hannahsq/PPS-50-DT/schematics/gpib_controller.kicad_sch

## KiCad design schematics/gpib_controller.kicad_sch (2026-04-03, an earlier design)

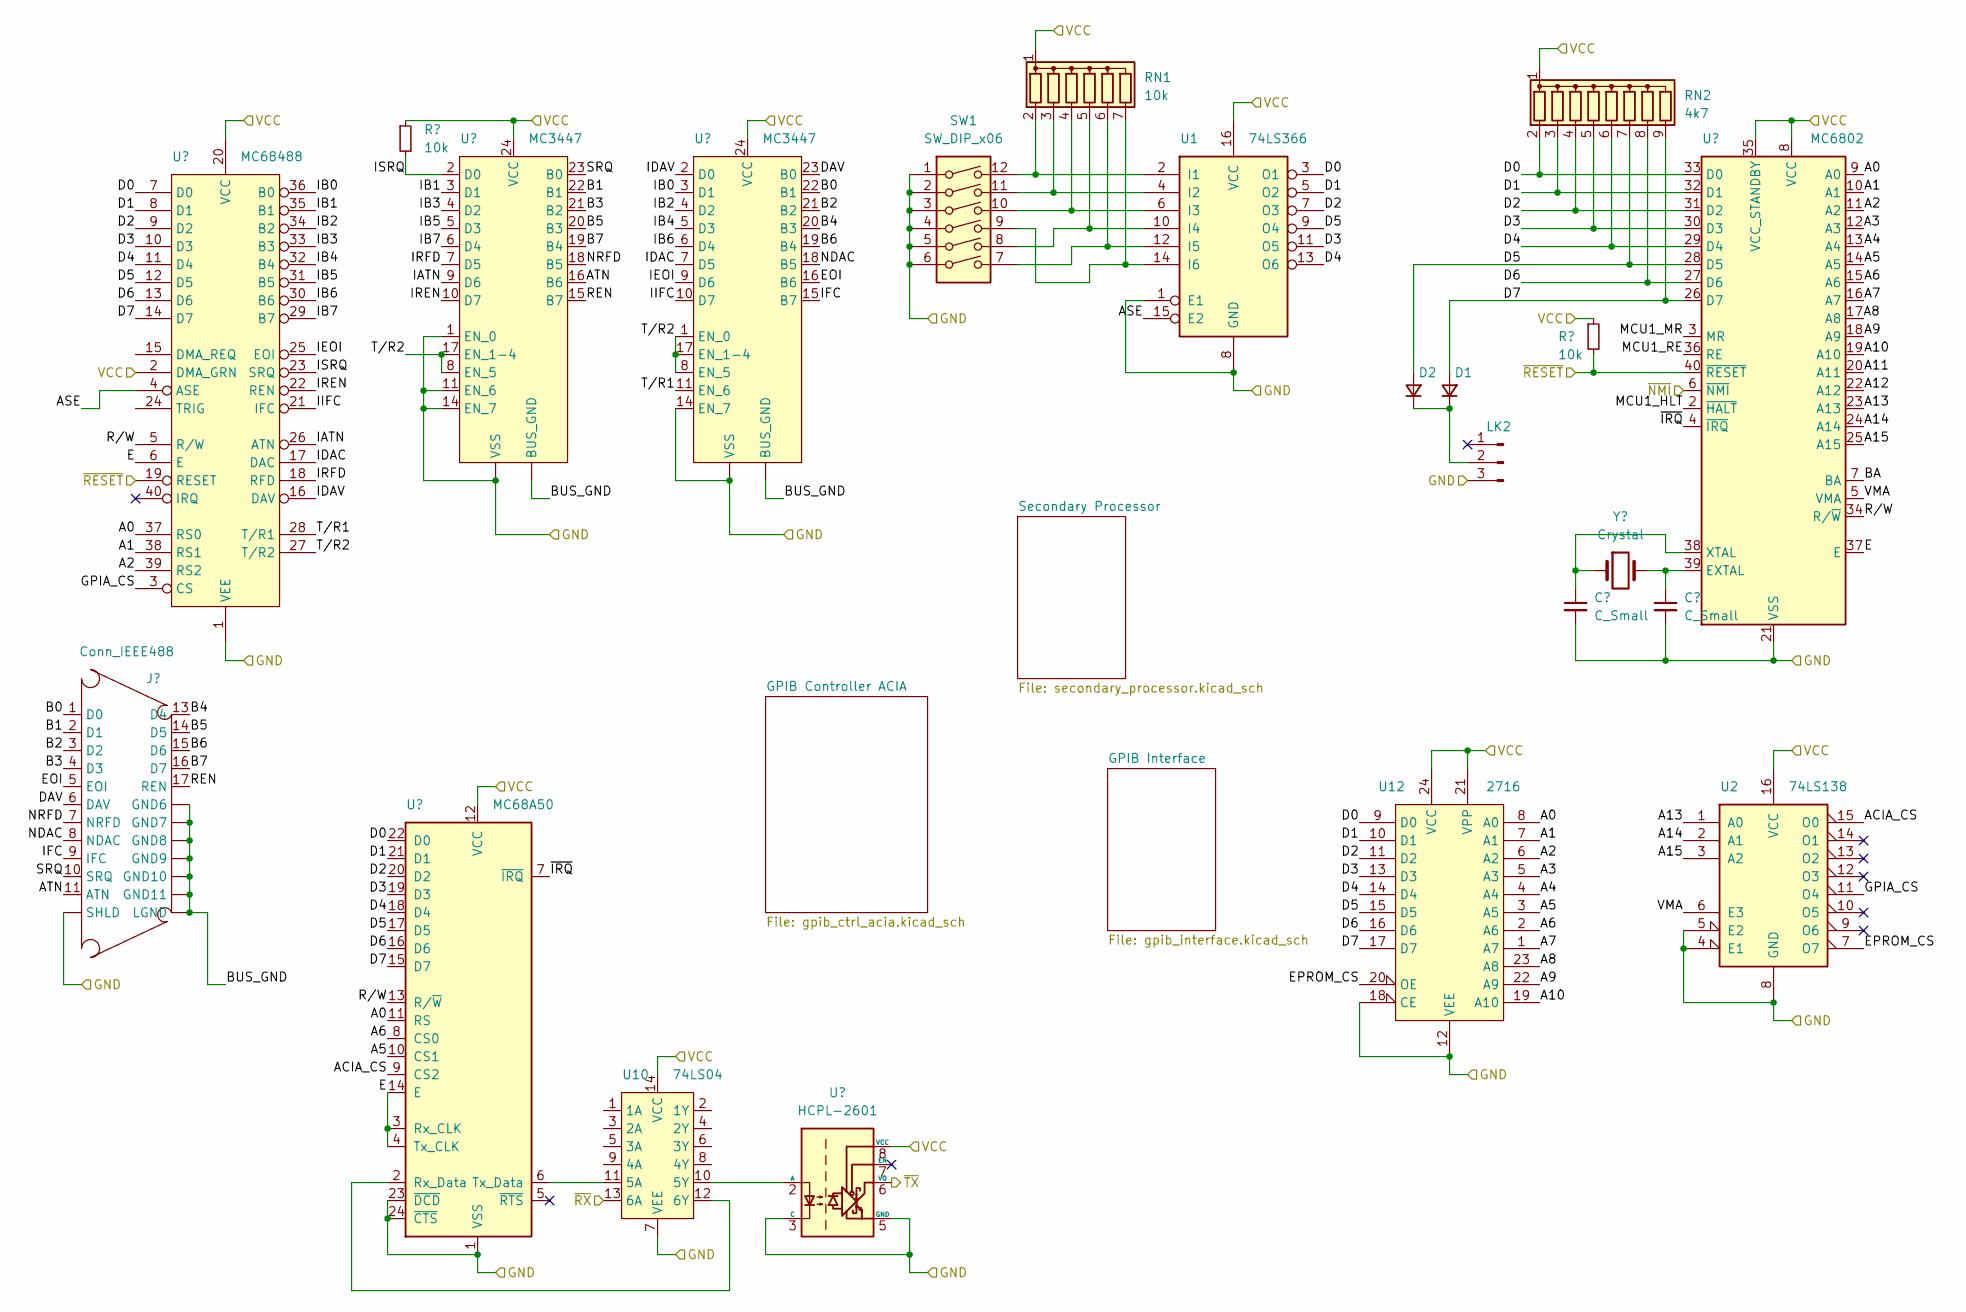
[picture p24: schematic gpib_controller.kicad_sch]

Parts:
D1, D2: D_Small
LK2: Conn_01x03_Male
RN1: 10k; R_Array_SIP7
RN2: 4k7; R_Array_SIP9
SW1: SW_DIP_x06
U1: 74LS366
U2: 74LS138
U10: 74LS04
U12: 2716

Connections:
A0: U12.8 (A0)
A1: U12.7 (A1)
A2: U12.6 (A2)
A3: U12.5 (A3)
A4: U12.4 (A4)
A5: U12.3 (A5)
A6: U12.2 (A6)
A7: U12.1 (A7)
A8: U12.23 (A8)
A9: U12.22 (A9)
A10: U12.19 (A10)
A13: U2.1 (A0)
A14: U2.2 (A1)
A15: U2.3 (A2)
ACIA_CS: U2.15 (O0)
ASE: U1.15 (E2)
D0: RN2.2 (R1), U1.3 (O1), U12.9 (D0)
D1: RN2.3 (R2), U1.5 (O2), U12.10 (D1)
D2: RN2.4 (R3), U1.7 (O3), U12.11 (D2)
D3: RN2.5 (R4), U1.11 (O5), U12.13 (D3)
D4: RN2.6 (R5), U1.13 (O6), U12.14 (D4)
D5: D2.2 (A), RN2.7 (R6), U1.9 (O4), U12.15 (D5)
D6: RN2.8 (R7), U12.16 (D6)
D7: D1.2 (A), RN2.9 (R8), U12.17 (D7)
EPROM_CS: U2.7 (O7), U12.20 (OE)
GND: LK2.3, SW1.1, SW1.2, SW1.3, SW1.4, SW1.5, SW1.6, U1.1 (E1), U1.8 (GND), U2.4 (E1), U2.5 (E2), U2.8 (GND), U10.7 (VEE), U12.12 (VEE), U12.18 (CE)
GPIA_CS: U2.11 (O4)
unnamed: D1.1 (K), D2.1 (K), LK2.2
unnamed: RN1.2 (R1), SW1.12, U1.2 (I1)
unnamed: RN1.3 (R2), SW1.11, U1.4 (I2)
unnamed: RN1.4 (R3), SW1.10, U1.6 (I3)
unnamed: RN1.5 (R4), SW1.8, U1.10 (I4)
unnamed: RN1.6 (R5), SW1.7, U1.12 (I5)
unnamed: RN1.7 (R6), SW1.9, U1.14 (I6)
VCC: RN1.1 (common), RN2.1 (common), U1.16 (VCC), U2.16 (VCC), U10.14 (VCC), U12.21 (VPP), U12.24 (VCC)
VMA: U2.6 (E3)
~RX: U10.13 (6A)
