hannahsq/PPS-50-DT/schematics/rect_and_reg.kicad_sch

## KiCad design schematics/rect_and_reg.kicad_sch (2024-05-18)

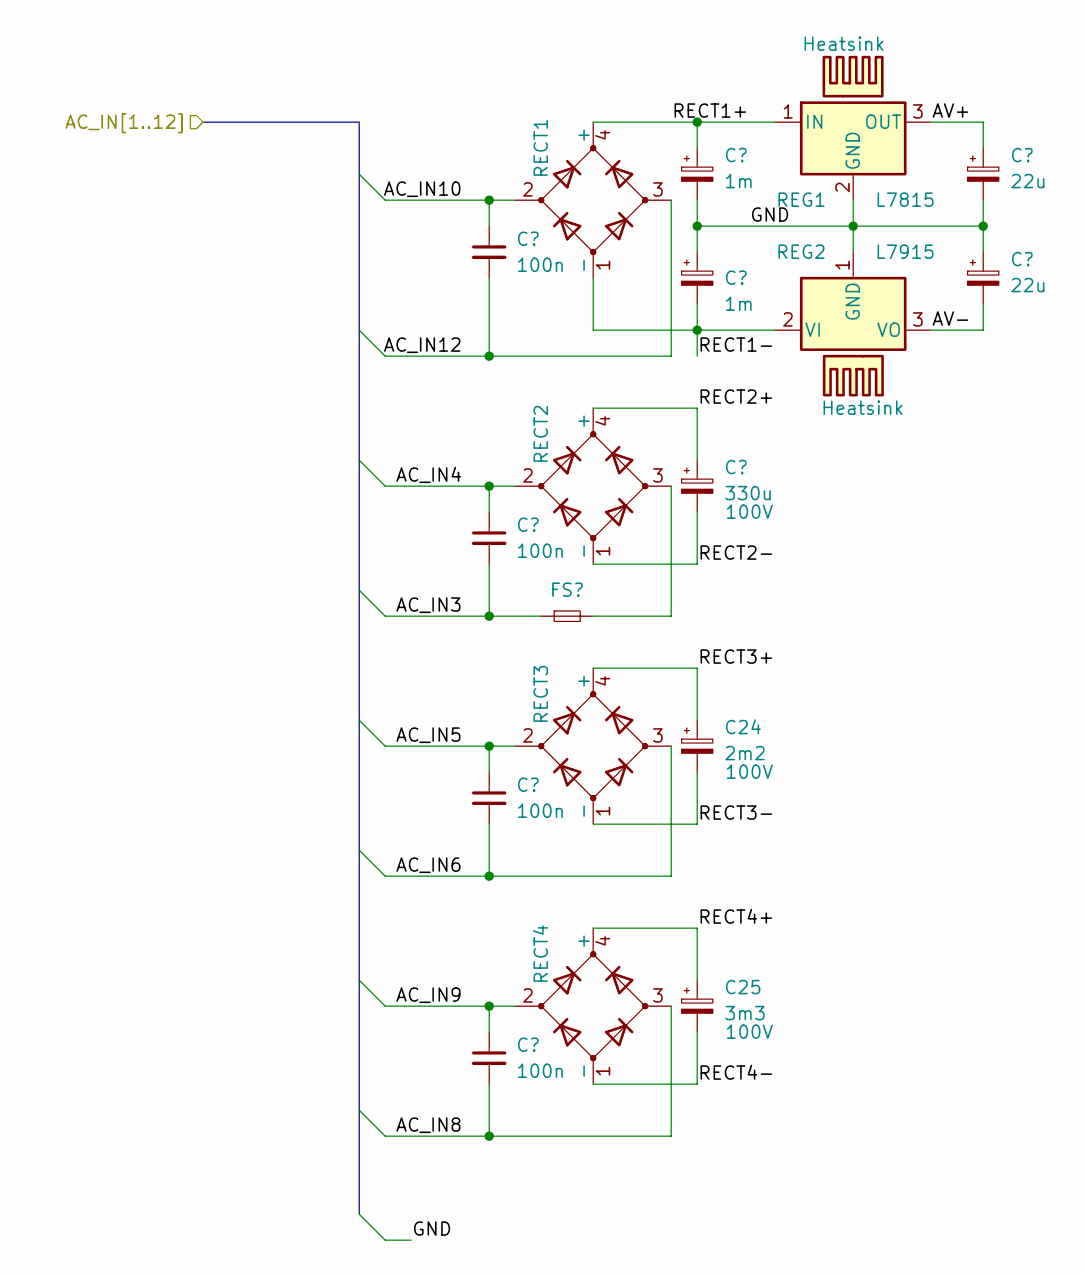
[picture p26: schematic rect_and_reg.kicad_sch]

Parts:
C24: 2m2; Voltage 100V
C25: 3m3; Voltage 100V
RECT1, RECT2, RECT3, RECT4: D_Bridge_-AA+
REG1: L7815
REG2: L7915

Connections:
AC_IN4: RECT2.2
AC_IN5: RECT3.2
AC_IN6: RECT3.3
AC_IN8: RECT4.3
AC_IN9: RECT4.2
AC_IN10: RECT1.2
AC_IN12: RECT1.3
AV+: REG1.3 (OUT)
AV-: REG2.3 (VO)
GND: REG1.2 (GND), REG2.1 (GND)
RECT1+: RECT1.4 (+), REG1.1 (IN)
RECT1-: RECT1.1 (-), REG2.2 (VI)
RECT2+: RECT2.4 (+)
RECT2-: RECT2.1 (-)
RECT3+: C24.1, RECT3.4 (+)
RECT3-: C24.2, RECT3.1 (-)
RECT4+: C25.1, RECT4.4 (+)
RECT4-: C25.2, RECT4.1 (-)
