hannahsq/PPS-50-DT/asm/primary_controller.asm

; f9dasm: M6800/1/2/3/8/9 / H6309 Binary/OS9/FLEX9 Disassembler V1.83
; Loaded binary file primary_controller.bin

;****************************************************
;* Used Labels                                      *
;****************************************************

irq_prescaler EQU     $0000
debounce_timer EQU     $0001
key_repeat_timer EQU     $0002
output_update_pending EQU     $0003
watchdog_counter EQU     $0004
tick_counter EQU     $0005
cha_voltage_set_hi EQU     $0006
cha_voltage_set_lo EQU     $0007
cha_current_set_hi EQU     $0008
cha_voltage_limit_hi EQU     $000A
cha_current_limit_hi EQU     $000C
cha_vs_shadow_hi EQU     $000E
cha_vs_shadow_lo EQU     $000F
cha_is_shadow_hi EQU     $0010
cha_is_shadow_lo EQU     $0011
chb_voltage_set_hi EQU     $0012
chb_current_set_hi EQU     $0014
chb_voltage_limit_hi EQU     $0016
chb_current_limit_hi EQU     $0018
chb_vs_shadow_hi EQU     $001A
chb_vs_shadow_lo EQU     $001B
chb_is_shadow_hi EQU     $001C
chb_is_shadow_lo EQU     $001D
adc_digit_0 EQU     $001E
adc_digit_1 EQU     $001F
adc_digit_2 EQU     $0020
adc_digit_3 EQU     $0021
adc_digit_4 EQU     $0022
adc_mux_channel EQU     $0023
dac_out_cha_v EQU     $0024
dac_out_cha_i EQU     $0025
dac_out_chb_v EQU     $0026
dac_out_chb_i EQU     $0027
dac_out_cha_vl EQU     $0028
dac_out_cha_il EQU     $0029
dac_out_chb_vl EQU     $002A
dac_out_chb_il EQU     $002B
dac_mux_ptr_hi EQU     $002C
M002D   EQU     $002D
dac_mux_select EQU     $002E
cha_fb_voltage_hi EQU     $002F
cha_fb_voltage_lo EQU     $0030
cha_fb_current_hi EQU     $0031
chb_fb_voltage_hi EQU     $0033
chb_fb_voltage_lo EQU     $0034
chb_fb_current_hi EQU     $0035
uart_timeout_lo EQU     $0037
uart_timeout_hi EQU     $0038
acia_rx_cmd EQU     $0039
acia_rx_data_hi EQU     $003A
acia_rx_data_lo EQU     $003B
math_temp_hi EQU     $003C
math_temp_lo EQU     $003D
acia_tx_cmd EQU     $003E
acia_tx_data_hi EQU     $003F
acia_tx_data_lo EQU     $0040
gpib_link_active EQU     $0041
reinit_requested EQU     $0042
keycode_or_adcmode EQU     $0043
key_state_flags EQU     $0044
scan_column_index EQU     $0045
scan_column_mask EQU     $0046
scan_result_offset EQU     $0047
scan_hit_count EQU     $0048
polarity_sign EQU     $0049
cmd_state_step EQU     $004A
digit_buf_0 EQU     $004B
digit_buf_1 EQU     $004C
digit_buf_2 EQU     $004D
digit_buf_3 EQU     $004E
decimal_point_pos EQU     $004F
digit_count EQU     $0050
channel_mode_state EQU     $0051
cmd_flags EQU     $0052
device_state EQU     $0053
status_pending EQU     $0054
status_confirmed EQU     $0055
uart_frame_type EQU     $0056
dac_mux_shadow EQU     $0057
display_port_shadow EQU     $0058
math_work_hi EQU     $0059
math_work_lo EQU     $005A
temp_ptr_hi EQU     $005B
temp_ptr_lo EQU     $005C
temp_counter EQU     $005D
indirect_ptr_hi EQU     $005E
indirect_ptr_lo EQU     $005F
dac_scale_result EQU     $0060
scale_input_hi EQU     $0061
scale_input_lo EQU     $0062
acia_inhibit_timer EQU     $0063
status_send_delay EQU     $0064
status_toggle EQU     $0065
dac_update_mask EQU     $0066
dac_settle_timer EQU     $0067
display_scan_index EQU     $0068
M007F   EQU     $007F
DAC_LATCH EQU     $0080
IC20_PRA EQU     $0090
IC20_CRA EQU     $0091
IC20_PRB EQU     $0092
IC20_CRB EQU     $0093
IC18_PRA EQU     $00A0
IC18_CRA EQU     $00A1
IC18_PRB EQU     $00A2
IC18_CRB EQU     $00A3
AMUX_SELECT EQU     $00C0
ACIA_CSR EQU     $00D0
ACIA_DR EQU     $00D1
IC19_PRA EQU     $00E0
IC19_CRA EQU     $00E1
IC19_PRB EQU     $00E2
IC19_CRB EQU     $00E3
M03E8   EQU     $03E8
M05DC   EQU     $05DC
range_threshold_50V EQU     $0898
M09F4   EQU     $09F4
M0F0F   EQU     $0F0F
range_threshold_25V EQU     $1130
M8F8F   EQU     $8F8F
MA4F0   EQU     $A4F0
MC7F0   EQU     $C7F0
MCEF1   EQU     $CEF1

;****************************************************
;* Program Code / Data Areas                        *
;****************************************************

        ORG     $E000

; === ACIA INTERRUPT HANDLER ===
; Increment GPIB activity counter (M0x04)
hdlr_ACIA_IRQ LDAA    watchdog_counter         ;E000: 96 04          '..'
        CMPA    #$FF                     ;E002: 81 FF          '..'
        BLS     ZE008                    ;E004: 23 02          '#.'
        BRA     ZE00B                    ;E006: 20 03          ' .'

ZE008   INC     >watchdog_counter        ;E008: 7C 00 04       '|..'
; Set ACIA inhibit timer to 0x14
ZE00B   LDAA    #$14                     ;E00B: 86 14          '..'
        STAA    acia_inhibit_timer       ;E00D: 97 63          '.c'
        LDAA    #$11                     ;E00F: 86 11          '..'
; Disable ACIA RX interrupts temporarily
        STAA    >ACIA_CSR                ;E011: B7 00 D0       '...'
; Read received data byte from ACIA
        LDAA    >ACIA_DR                 ;E014: B6 00 D1       '...'
; Decode frame type (bits 3:2 determine status/data/cmd)
        JSR     decode_uart_frame_type   ;E017: BD E0 53       '..S'
        LDAB    uart_frame_type          ;E01A: D6 56          '.V'
; Send acknowledgment byte back to GPIB controller
        JSR     acia_send_byte           ;E01C: BD E0 99       '...'
        BNE     hdlr_ACIA_RTI            ;E01F: 26 28          '&('
; Receive 3-byte command from GPIB controller
        JSR     acia_recv_3_bytes        ;E021: BD E0 79       '..y'
        BNE     hdlr_ACIA_RTI            ;E024: 26 23          '&#'
; Load command byte
        LDAA    acia_rx_cmd              ;E026: 96 39          '.9'
; Check for 'q' (0x71) - query command
        CMPA    #$71                     ;E028: 81 71          '.q'
; Check for status commands: 'S'(0x53), 'T'(0x54), 'q'(0x71)
; These commands clear the GPIB link active flag
        BEQ     ZE037                    ;E02A: 27 0B          ''.'
        CMPA    #$53                     ;E02C: 81 53          '.S'
        BEQ     ZE037                    ;E02E: 27 07          ''.'
        CMPA    #$54                     ;E030: 81 54          '.T'
        BEQ     ZE037                    ;E032: 27 03          ''.'
        CLR     >gpib_link_active        ;E034: 7F 00 41       '..A'
; Reset command state variables
ZE037   JSR     reset_cmd_state          ;E037: BD F3 EA       '...'
; Clear command step counter
        CLR     >cmd_state_step          ;E03A: 7F 00 4A       '..J'
; Process command and build response
        JSR     process_gpib_command     ;E03D: BD E0 EE       '...'
; Send 3-byte response back to GPIB controller
        JSR     acia_send_3_bytes        ;E040: BD E0 CE       '...'
; Clear channel mode state bits
        CLR     >channel_mode_state      ;E043: 7F 00 51       '..Q'
        CLR     >cmd_flags               ;E046: 7F 00 52       '..R'
; Re-enable ACIA RX interrupts (write 0x91 to CSR)
hdlr_ACIA_RTI LDAA    #$00                     ;E049: 86 00          '..'
        LDAA    #$91                     ;E04B: 86 91          '..'
        STAA    >ACIA_CSR                ;E04D: B7 00 D0       '...'
; Return from interrupt
        JMP     hdlr_RTI                 ;E050: 7E E5 79       '~.y'

; === DECODE UART FRAME TYPE FROM RX BITS 3:2 ===
; Bits 3:2 == 00: normal data (frame_type = 0)
decode_uart_frame_type ANDA    #$0C                     ;E053: 84 0C          '..'
        BNE     ZE05C                    ;E055: 26 05          '&.'
        CLR     >uart_frame_type         ;E057: 7F 00 56       '..V'
        BRA     ZE078                    ;E05A: 20 1C          ' .'

; Bits 3:2 == 10: status update (frame_type = 1)
ZE05C   CMPA    #$08                     ;E05C: 81 08          '..'
        BNE     ZE066                    ;E05E: 26 06          '&.'
        LDAA    #$01                     ;E060: 86 01          '..'
        STAA    uart_frame_type          ;E062: 97 56          '.V'
        BRA     ZE078                    ;E064: 20 12          ' .'

; Bits 3:2 == 11: status + data (frame_type = 3)
ZE066   CMPA    #$0C                     ;E066: 81 0C          '..'
        BNE     ZE070                    ;E068: 26 06          '&.'
        LDAA    #$03                     ;E06A: 86 03          '..'
        STAA    uart_frame_type          ;E06C: 97 56          '.V'
        BRA     ZE078                    ;E06E: 20 08          ' .'

; Bits 3:2 == 01: data only (frame_type = 2)
ZE070   CMPA    #$04                     ;E070: 81 04          '..'
        BNE     ZE078                    ;E072: 26 04          '&.'
        LDAA    #$02                     ;E074: 86 02          '..'
        STAA    uart_frame_type          ;E076: 97 56          '.V'
ZE078   RTS                              ;E078: 39             '9'

;-------------------------------------------------------------------------------

; === RECV 3 BYTES FROM ACIA ===
; Receive bytes into acia_rx_cmd, acia_rx_data_hi, acia_rx_data_lo
; Returns Z=1 on success, Z=0 on timeout/error
acia_recv_3_bytes JSR     acia_recv_byte           ;E079: BD E0 B1       '...'
        BNE     ZE095                    ;E07C: 26 17          '&.'
        STAB    >acia_rx_cmd             ;E07E: F7 00 39       '..9'
        JSR     acia_recv_byte           ;E081: BD E0 B1       '...'
        BNE     ZE095                    ;E084: 26 0F          '&.'
        STAB    >acia_rx_data_hi         ;E086: F7 00 3A       '..:'
        JSR     acia_recv_byte           ;E089: BD E0 B1       '...'
        BNE     ZE095                    ;E08C: 26 07          '&.'
        STAB    >acia_rx_data_lo         ;E08E: F7 00 3B       '..;'
        CLRA                             ;E091: 4F             'O'
        JMP     ZE097                    ;E092: 7E E0 97       '~..'

ZE095   LDAA    #$FF                     ;E095: 86 FF          '..'
ZE097   TSTA                             ;E097: 4D             'M'
        RTS                              ;E098: 39             '9'

;-------------------------------------------------------------------------------

; === SEND BYTE VIA ACIA ===
; Wait for TX buffer empty, send byte from ACCB
acia_send_byte LDX     #uart_timeout_lo         ;E099: CE 00 37       '..7'
; Poll ACIA status for TDRE (bit 1)
ZE09C   LDAA    >ACIA_CSR                ;E09C: B6 00 D0       '...'
        ANDA    #$02                     ;E09F: 84 02          '..'
        BNE     ZE0AB                    ;E0A1: 26 08          '&.'
        DEX                              ;E0A3: 09             '.'
        BNE     ZE09C                    ;E0A4: 26 F6          '&.'
        LDAA    #$FF                     ;E0A6: 86 FF          '..'
        JMP     ZE0AF                    ;E0A8: 7E E0 AF       '~..'

; Write byte to ACIA data register
ZE0AB   STAB    >ACIA_DR                 ;E0AB: F7 00 D1       '...'
        CLRA                             ;E0AE: 4F             'O'
; Return Z=1 on success
ZE0AF   TSTA                             ;E0AF: 4D             'M'
        RTS                              ;E0B0: 39             '9'

;-------------------------------------------------------------------------------

; === RECV BYTE FROM ACIA ===
; Wait for RX buffer full, receive byte into ACCB
acia_recv_byte LDX     #uart_timeout_lo         ;E0B1: CE 00 37       '..7'
ZE0B4   LDAA    >ACIA_CSR                ;E0B4: B6 00 D0       '...'
        TAB                              ;E0B7: 16             '.'
        ANDA    #$01                     ;E0B8: 84 01          '..'
        BNE     ZE0C4                    ;E0BA: 26 08          '&.'
        DEX                              ;E0BC: 09             '.'
        BNE     ZE0B4                    ;E0BD: 26 F5          '&.'
; Return Z=0 on timeout
ZE0BF   LDAA    #$FF                     ;E0BF: 86 FF          '..'
        JMP     ZE0C9                    ;E0C1: 7E E0 C9       '~..'

; Return Z=0 on ACIA error
ZE0C4   ANDB    #$70                     ;E0C4: C4 70          '.p'
        BNE     ZE0BF                    ;E0C6: 26 F7          '&.'
        CLRA                             ;E0C8: 4F             'O'
; Return Z=1 on success
ZE0C9   LDAB    >ACIA_DR                 ;E0C9: F6 00 D1       '...'
        TSTA                             ;E0CC: 4D             'M'
        RTS                              ;E0CD: 39             '9'

;-------------------------------------------------------------------------------

; === SEND 3 BYTES VIA ACIA ===
; Send acia_tx_cmd, acia_tx_data_hi, acia_tx_data_lo
acia_send_3_bytes LDAB    >acia_tx_cmd             ;E0CE: F6 00 3E       '..>'
        JSR     acia_send_byte           ;E0D1: BD E0 99       '...'
        BNE     ZE0EA                    ;E0D4: 26 14          '&.'
        LDAB    >acia_tx_data_hi         ;E0D6: F6 00 3F       '..?'
        JSR     acia_send_byte           ;E0D9: BD E0 99       '...'
        BNE     ZE0EA                    ;E0DC: 26 0C          '&.'
        LDAB    >acia_tx_data_lo         ;E0DE: F6 00 40       '..@'
        JSR     acia_send_byte           ;E0E1: BD E0 99       '...'
        BNE     ZE0EA                    ;E0E4: 26 04          '&.'
        CLRA                             ;E0E6: 4F             'O'
        JMP     ZE0EC                    ;E0E7: 7E E0 EC       '~..'

ZE0EA   LDAA    #$FF                     ;E0EA: 86 FF          '..'
ZE0EC   TSTA                             ;E0EC: 4D             'M'
        RTS                              ;E0ED: 39             '9'

;-------------------------------------------------------------------------------

; === PROCESS GPIB COMMAND ===
; Copy RX buffer to TX buffer (echo command)
process_gpib_command LDAA    >acia_rx_cmd             ;E0EE: B6 00 39       '..9'
        STAA    >acia_tx_cmd             ;E0F1: B7 00 3E       '..>'
        LDAA    >acia_rx_data_hi         ;E0F4: B6 00 3A       '..:'
        STAA    >acia_tx_data_hi         ;E0F7: B7 00 3F       '..?'
        LDAA    >acia_rx_data_lo         ;E0FA: B6 00 3B       '..;'
        STAA    >acia_tx_data_lo         ;E0FD: B7 00 40       '..@'
; Test frame_type: if even, check for special commands
        LDAA    >uart_frame_type         ;E100: B6 00 56       '..V'
        ANDA    #$01                     ;E103: 84 01          '..'
        BNE     gpib_cmd_dispatch        ;E105: 26 18          '&.'
; Check for 'S' (0x53): serial poll �¨ enable remote
        LDAA    >acia_rx_cmd             ;E107: B6 00 39       '..9'
        CMPA    #$53                     ;E10A: 81 53          '.S'
        BEQ     ZE11A                    ;E10C: 27 0C          ''.'
; Check for 'U' (0x55): status update
        CMPA    #$55                     ;E10E: 81 55          '.U'
        BEQ     gpib_cmd_dispatch        ;E110: 27 0D          ''.'
; Check for 'V' (0x56): device clear
        CMPA    #$56                     ;E112: 81 56          '.V'
        BEQ     gpib_cmd_dispatch        ;E114: 27 09          ''.'
        LDAA    #$01                     ;E116: 86 01          '..'
        BRA     gpib_cmd_dispatch        ;E118: 20 05          ' .'

ZE11A   JMP     cmd_enable_remote        ;E11A: 7E E2 9E       '~..'

        BRA     ZE14D                    ;E11D: 20 2E          ' .'

; === COMMAND DISPATCH VIA JUMP TABLE ===
gpib_cmd_dispatch LDAA    >acia_rx_cmd             ;E11F: B6 00 39       '..9'
; Subtract 'A' (0x41) from command byte to get table index
        SUBA    #$41                     ;E122: 80 41          '.A'
        TAB                              ;E124: 16             '.'
; Double index for 16-bit pointers (ASLB)
        ASLB                             ;E125: 58             'X'
; Check bounds: index must be <= 0x31 (commands 'A'-'r')
        CMPA    #$31                     ;E126: 81 31          '.1'
        BHI     ZE148                    ;E128: 22 1E          '".'
        CLRA                             ;E12A: 4F             'O'
; Load jump address from table at E14F + index
        LDX     #CMD_JUMP_TABLE          ;E12B: CE E1 4F       '..O'
        STX     >indirect_ptr_hi         ;E12E: FF 00 5E       '..^'
        ADDB    >indirect_ptr_lo         ;E131: FB 00 5F       '.._'
        STAB    >indirect_ptr_lo         ;E134: F7 00 5F       '.._'
        ADCA    >indirect_ptr_hi         ;E137: B9 00 5E       '..^'
        STAA    >indirect_ptr_hi         ;E13A: B7 00 5E       '..^'
        LDX     >indirect_ptr_hi         ;E13D: FE 00 5E       '..^'
        LDX     ,X                       ;E140: EE 00          '..'
        CLRA                             ;E142: 4F             'O'
; Jump to command handler
        JMP     ,X                       ;E143: 6E 00          'n.'

        JMP     ZE14D                    ;E145: 7E E1 4D       '~.M'

ZE148   LDAA    #$4D                     ;E148: 86 4D          '.M'
        JMP     cmd_respond_error_or_echo ;E14A: 7E E1 B3       '~..'

ZE14D   TSTA                             ;E14D: 4D             'M'
        RTS                              ;E14E: 39             '9'

;-------------------------------------------------------------------------------

; === COMMAND JUMP TABLE ===
; Entries 0-7 ('A'-'H'): cmd_process_set_value (voltage/current set)
CMD_JUMP_TABLE FDB     cmd_process_set_value    ;E14F: E2 A7          '..'
        FDB     cmd_process_set_value    ;E151: E2 A7          '..'
        FDB     cmd_process_set_value    ;E153: E2 A7          '..'
        FDB     cmd_process_set_value    ;E155: E2 A7          '..'
        FDB     cmd_process_set_value    ;E157: E2 A7          '..'
        FDB     cmd_process_set_value    ;E159: E2 A7          '..'
        FDB     cmd_process_set_value    ;E15B: E2 A7          '..'
        FDB     cmd_process_set_value    ;E15D: E2 A7          '..'
; Entry 8 ('I'): cmd_set_cha_cv_mode
        FDB     cmd_set_cha_cv_mode      ;E15F: E2 3F          '.?'
; Entry 9 ('J'): cmd_set_cha_cc_mode
        FDB     cmd_set_cha_cc_mode      ;E161: E2 4C          '.L'
; Entry 10 ('K'): cmd_set_cha_il_mode
        FDB     cmd_set_cha_il_mode      ;E163: E2 59          '.Y'
; Entry 11 ('L'): cmd_set_cha_vl_mode
        FDB     cmd_set_cha_vl_mode      ;E165: E2 66          '.f'
; Entry 12 ('M'): cmd_set_dac_value (readback ChA)
        FDB     ME432_via_cvec_e167      ;E167: E4 32          '.2'
; Entry 13 ('N'): cmd_set_dac_value (readback ChA alt)
        FDB     ME43F_via_cvec_e169      ;E169: E4 3F          '.?'
; Entry 14 ('O'): cmd_set_dac_value (readback ChB)
        FDB     ME44C_via_cvec_e16b      ;E16B: E4 4C          '.L'
; Entry 15 ('P'): cmd_set_dac_value (readback ChB alt)
        FDB     ME459_via_cvec_e16d      ;E16D: E4 59          '.Y'
; Entry 16 ('Q'): cmd_enable_tracking
        FDB     cmd_enable_tracking      ;E16F: E1 EF          '..'
; Entry 17 ('R'): cmd_disable_tracking
        FDB     cmd_disable_tracking     ;E171: E2 36          '.6'
; Entry 18 ('S'): cmd_enable_remote
        FDB     cmd_enable_remote        ;E173: E2 9E          '..'
; Entry 19 ('T'): cmd_update_status_echo
        FDB     cmd_update_status_echo   ;E175: E1 C9          '..'
; Entry 20 ('U'): cmd_set_frame_type_3
        FDB     cmd_set_frame_type_3     ;E177: E1 D6          '..'
; Entry 21 ('V'): cmd_set_reinit_flag
        FDB     cmd_set_reinit_flag      ;E179: E3 90          '..'
; Entry 22-23 ('W','X'): cmd_respond_error
        FDB     cmd_respond_error_or_echo ;E17B: E1 B3          '..'
        FDB     cmd_respond_error_or_echo ;E17D: E1 B3          '..'
; Entry 24 ('Y'): cmd_enable_output
        FDB     cmd_enable_output        ;E17F: E1 DD          '..'
; Entry 25 ('Z'): cmd_disable_output
        FDB     cmd_disable_output       ;E181: E1 E6          '..'
        FDB     cmd_respond_error_or_echo ;E183: E1 B3          '..'
        FDB     cmd_respond_error_or_echo ;E185: E1 B3          '..'
        FDB     cmd_respond_error_or_echo ;E187: E1 B3          '..'
        FDB     cmd_respond_error_or_echo ;E189: E1 B3          '..'
        FDB     cmd_respond_error_or_echo ;E18B: E1 B3          '..'
        FDB     cmd_respond_error_or_echo ;E18D: E1 B3          '..'
        FDB     cmd_set_dac_value        ;E18F: E2 8C          '..'
        FDB     cmd_set_dac_value        ;E191: E2 8C          '..'
        FDB     cmd_set_dac_value        ;E193: E2 8C          '..'
        FDB     cmd_set_dac_value        ;E195: E2 8C          '..'
        FDB     cmd_set_dac_value        ;E197: E2 8C          '..'
        FDB     cmd_set_dac_value        ;E199: E2 8C          '..'
        FDB     cmd_set_dac_value        ;E19B: E2 8C          '..'
        FDB     cmd_set_dac_value        ;E19D: E2 8C          '..'
        FDB     cmd_set_dac_value        ;E19F: E2 8C          '..'
        FDB     cmd_set_dac_value        ;E1A1: E2 8C          '..'
        FDB     cmd_set_dac_value        ;E1A3: E2 8C          '..'
        FDB     cmd_set_dac_value        ;E1A5: E2 8C          '..'
        FDB     cmd_respond_error_or_echo ;E1A7: E1 B3          '..'
        FDB     cmd_respond_error_or_echo ;E1A9: E1 B3          '..'
        FDB     cmd_respond_error_or_echo ;E1AB: E1 B3          '..'
        FDB     cmd_respond_error_or_echo ;E1AD: E1 B3          '..'
; Entry 48 ('q'): cmd_read_state
        FDB     cmd_read_state           ;E1AF: E2 73          '.s'
; Entry 49 ('r'): cmd_read_version
        FDB     cmd_read_version         ;E1B1: E2 7E          '.~'
; === ERROR/ECHO RESPONSE ===
; Set bit 7 of response byte (error flag)
cmd_respond_error_or_echo TSTA                             ;E1B3: 4D             'M'
        BNE     ZE1B8                    ;E1B4: 26 02          '&.'
        LDAA    #$4D                     ;E1B6: 86 4D          '.M'
ZE1B8   ORAA    #$80                     ;E1B8: 8A 80          '..'
; Store in TX buffer for GPIB response
        STAA    acia_tx_cmd              ;E1BA: 97 3E          '.>'
; Set error status in M0x52
        LDAA    #$80                     ;E1BC: 86 80          '..'
        STAA    cmd_flags                ;E1BE: 97 52          '.R'
; Clear UART timeout counters
        CLR     >uart_timeout_lo         ;E1C0: 7F 00 37       '..7'
        CLR     >uart_timeout_hi         ;E1C3: 7F 00 38       '..8'
        JMP     cold_start_entry         ;E1C6: 7E E4 63       '~.c'

cmd_update_status_echo LDAA    status_confirmed         ;E1C9: 96 55          '.U'
        STAA    status_pending           ;E1CB: 97 54          '.T'
        LDAA    uart_frame_type          ;E1CD: 96 56          '.V'
        ANDA    #$02                     ;E1CF: 84 02          '..'
        STAA    uart_frame_type          ;E1D1: 97 56          '.V'
        JMP     cold_start_entry         ;E1D3: 7E E4 63       '~.c'

cmd_set_frame_type_3 LDAA    #$03                     ;E1D6: 86 03          '..'
        STAA    uart_frame_type          ;E1D8: 97 56          '.V'
        JMP     cold_start_entry         ;E1DA: 7E E4 63       '~.c'

cmd_enable_output LDAA    device_state             ;E1DD: 96 53          '.S'
        ORAA    #$40                     ;E1DF: 8A 40          '.@'
        STAA    device_state             ;E1E1: 97 53          '.S'
        JMP     cold_start_entry         ;E1E3: 7E E4 63       '~.c'

cmd_disable_output LDAA    device_state             ;E1E6: 96 53          '.S'
        ANDA    #$BF                     ;E1E8: 84 BF          '..'
        STAA    device_state             ;E1EA: 97 53          '.S'
        JMP     cold_start_entry         ;E1EC: 7E E4 63       '~.c'

; === ENABLE TRACKING ===
; Set bit 7 of device_state (tracking enabled)
cmd_enable_tracking LDAA    device_state             ;E1EF: 96 53          '.S'
        ORAA    #$80                     ;E1F1: 8A 80          '..'
        STAA    device_state             ;E1F3: 97 53          '.S'
; Copy Channel A setpoints to Channel B
        LDX     #cha_voltage_set_lo      ;E1F5: CE 00 07       '...'
ZE1F8   LDAA    $06,X                    ;E1F8: A6 06          '..'
        STAA    $12,X                    ;E1FA: A7 12          '..'
        DEX                              ;E1FC: 09             '.'
        BNE     ZE1F8                    ;E1FD: 26 F9          '&.'
        LDAA    cha_voltage_set_hi       ;E1FF: 96 06          '..'
        STAA    chb_voltage_set_hi       ;E201: 97 12          '..'
        LDAA    device_state             ;E203: 96 53          '.S'
        ANDA    #$95                     ;E205: 84 95          '..'
        TAB                              ;E207: 16             '.'
        ASLB                             ;E208: 58             'X'
        ANDB    #$02                     ;E209: C4 02          '..'
        ABA                              ;E20B: 1B             '.'
        STAA    device_state             ;E20C: 97 53          '.S'
        BITA    #$02                     ;E20E: 85 02          '..'
        BEQ     ZE21A                    ;E210: 27 08          ''.'
        LDAA    #$E6                     ;E212: 86 E6          '..'
        STAA    dac_settle_timer         ;E214: 97 67          '.g'
        LDAA    #$60                     ;E216: 86 60          '.`'
        BRA     ZE220                    ;E218: 20 06          ' .'

ZE21A   LDAA    #$C6                     ;E21A: 86 C6          '..'
        STAA    dac_settle_timer         ;E21C: 97 67          '.g'
        LDAA    #$90                     ;E21E: 86 90          '..'
ZE220   STAA    dac_update_mask          ;E220: 97 66          '.f'
        JSR     dac_update_all           ;E222: BD EB E2       '...'
        LDAA    status_confirmed         ;E225: 96 55          '.U'
        ANDA    #$0F                     ;E227: 84 0F          '..'
        TAB                              ;E229: 16             '.'
        ASLB                             ;E22A: 58             'X'
        ASLB                             ;E22B: 58             'X'
        ASLB                             ;E22C: 58             'X'
        ASLB                             ;E22D: 58             'X'
        ABA                              ;E22E: 1B             '.'
        STAA    status_confirmed         ;E22F: 97 55          '.U'
        STAA    status_pending           ;E231: 97 54          '.T'
        JMP     cold_start_entry         ;E233: 7E E4 63       '~.c'

; === DISABLE TRACKING ===
; Clear bit 7 of device_state
cmd_disable_tracking LDAA    device_state             ;E236: 96 53          '.S'
        ANDA    #$7F                     ;E238: 84 7F          '..'
        STAA    device_state             ;E23A: 97 53          '.S'
        JMP     cold_start_entry         ;E23C: 7E E4 63       '~.c'

cmd_set_cha_cv_mode LDAA    status_confirmed         ;E23F: 96 55          '.U'
        ANDA    #$F0                     ;E241: 84 F0          '..'
        ORAA    #$04                     ;E243: 8A 04          '..'
        STAA    status_confirmed         ;E245: 97 55          '.U'
        STAA    status_pending           ;E247: 97 54          '.T'
        JMP     cold_start_entry         ;E249: 7E E4 63       '~.c'

cmd_set_cha_cc_mode LDAA    status_confirmed         ;E24C: 96 55          '.U'
        ANDA    #$0F                     ;E24E: 84 0F          '..'
        ORAA    #$40                     ;E250: 8A 40          '.@'
        STAA    status_confirmed         ;E252: 97 55          '.U'
        STAA    status_pending           ;E254: 97 54          '.T'
        JMP     cold_start_entry         ;E256: 7E E4 63       '~.c'

cmd_set_cha_il_mode LDAA    status_confirmed         ;E259: 96 55          '.U'
        ANDA    #$F0                     ;E25B: 84 F0          '..'
        ORAA    #$05                     ;E25D: 8A 05          '..'
        STAA    status_confirmed         ;E25F: 97 55          '.U'
        STAA    status_pending           ;E261: 97 54          '.T'
        JMP     cold_start_entry         ;E263: 7E E4 63       '~.c'

cmd_set_cha_vl_mode LDAA    status_confirmed         ;E266: 96 55          '.U'
        ANDA    #$0F                     ;E268: 84 0F          '..'
        ORAA    #$50                     ;E26A: 8A 50          '.P'
        STAA    status_confirmed         ;E26C: 97 55          '.U'
        STAA    status_pending           ;E26E: 97 54          '.T'
        JMP     cold_start_entry         ;E270: 7E E4 63       '~.c'

; === READ STATE COMMAND ===
; Copy device_state and status_pending to TX buffer
cmd_read_state LDAA    device_state             ;E273: 96 53          '.S'
        STAA    acia_tx_data_hi          ;E275: 97 3F          '.?'
        LDAA    status_pending           ;E277: 96 54          '.T'
        STAA    acia_tx_data_lo          ;E279: 97 40          '.@'
        JMP     cold_start_entry         ;E27B: 7E E4 63       '~.c'

; === READ VERSION ===
; Return version string (0x31, 0x31)
cmd_read_version LDAA    #$31                     ;E27E: 86 31          '.1'
        STAA    acia_tx_data_hi          ;E280: 97 3F          '.?'
        LDAA    #$31                     ;E282: 86 31          '.1'
        STAA    acia_tx_data_lo          ;E284: 97 40          '.@'
        JMP     cold_start_entry         ;E286: 7E E4 63       '~.c'

        JMP     cold_start_entry         ;E289: 7E E4 63       '~.c'

cmd_set_dac_value LDAA    acia_rx_cmd              ;E28C: 96 39          '.9'
        SUBA    #$61                     ;E28E: 80 61          '.a'
        BITA    #$01                     ;E290: 85 01          '..'
        BEQ     ZE298                    ;E292: 27 04          ''.'
        ADDA    #$0C                     ;E294: 8B 0C          '..'
        ANDA    #$FE                     ;E296: 84 FE          '..'
ZE298   JSR     cmd_read_dac_channel     ;E298: BD E3 97       '...'
        JMP     cold_start_entry         ;E29B: 7E E4 63       '~.c'

cmd_enable_remote LDAA    uart_frame_type          ;E29E: 96 56          '.V'
        ORAA    #$01                     ;E2A0: 8A 01          '..'
        STAA    uart_frame_type          ;E2A2: 97 56          '.V'
        JMP     cold_start_entry         ;E2A4: 7E E4 63       '~.c'

; === PROCESS SET VALUE (commands A-H) ===
; Subtract 'A' from command byte to get channel/function index
cmd_process_set_value LDAA    acia_rx_cmd              ;E2A7: 96 39          '.9'
        SUBA    #$41                     ;E2A9: 80 41          '.A'
; Mask to 3-bit index
        ANDA    #$07                     ;E2AB: 84 07          '..'
; Check bit 2: if set, it's a limit command (E-H)
        BITA    #$04                     ;E2AD: 85 04          '..'
        BEQ     ZE2B8                    ;E2AF: 27 07          ''.'
        ANDA    #$02                     ;E2B1: 84 02          '..'
        LSRA                             ;E2B3: 44             'D'
        ADDA    #$04                     ;E2B4: 8B 04          '..'
        BRA     ZE2C8                    ;E2B6: 20 10          ' .'

; Check tracking state
ZE2B8   LDAB    device_state             ;E2B8: D6 53          '.S'
        BITB    #$80                     ;E2BA: C5 80          '..'
        BEQ     ZE2C7                    ;E2BC: 27 09          ''.'
        BITA    #$01                     ;E2BE: 85 01          '..'
        BEQ     ZE2C7                    ;E2C0: 27 05          ''.'
        LDAA    #$54                     ;E2C2: 86 54          '.T'
        JMP     ZE1B8                    ;E2C4: 7E E1 B8       '~..'

ZE2C7   LSRA                             ;E2C7: 44             'D'
; Shift data value (left shift acia_rx_data by 1)
ZE2C8   ASL     >acia_rx_data_lo         ;E2C8: 78 00 3B       'x.;'
        ROL     >acia_rx_data_hi         ;E2CB: 79 00 3A       'y.:'
; Check range limits via F7DB
        JSR     check_dac_range_50v      ;E2CE: BD F7 DB       '...'
        BCS     ZE2D8                    ;E2D1: 25 05          '%.'
        LDAA    #$4E                     ;E2D3: 86 4E          '.N'
        JMP     ZE1B8                    ;E2D5: 7E E1 B8       '~..'

; Store set value in appropriate DAC register
ZE2D8   LDX     #cha_voltage_set_hi      ;E2D8: CE 00 06       '...'
        LDAA    acia_rx_cmd              ;E2DB: 96 39          '.9'
        SUBA    #$41                     ;E2DD: 80 41          '.A'
        BITA    #$01                     ;E2DF: 85 01          '..'
        BEQ     ZE2E6                    ;E2E1: 27 03          ''.'
        LDX     #chb_voltage_set_hi      ;E2E3: CE 00 12       '...'
; Apply mode/state mask
ZE2E6   ANDA    #$06                     ;E2E6: 84 06          '..'
        JSR     cmd_store_and_convert    ;E2E8: BD E3 AF       '...'
        LDAA    #$44                     ;E2EB: 86 44          '.D'
        SUBA    acia_rx_cmd              ;E2ED: 90 39          '.9'
        BMI     ZE333                    ;E2EF: 2B 42          '+B'
        TAB                              ;E2F1: 16             '.'
        ASLB                             ;E2F2: 58             'X'
        ASLB                             ;E2F3: 58             'X'
        ABA                              ;E2F4: 1B             '.'
; Look up DAC scaling from table at E378
        LDX     #DAC_CLIP_TABLE_A        ;E2F5: CE E3 78       '..x'
        STX     indirect_ptr_hi          ;E2F8: DF 5E          '.^'
        ADDA    indirect_ptr_lo          ;E2FA: 9B 5F          '._'
        STAA    indirect_ptr_lo          ;E2FC: 97 5F          '._'
        LDX     indirect_ptr_hi          ;E2FE: DE 5E          '.^'
        LDAA    ,X                       ;E300: A6 00          '..'
        STAA    dac_update_mask          ;E302: 97 66          '.f'
        LDAA    acia_rx_cmd              ;E304: 96 39          '.9'
        CMPA    #$42                     ;E306: 81 42          '.B'
        BHI     ZE312                    ;E308: 22 08          '".'
        ANDA    #$03                     ;E30A: 84 03          '..'
        BITA    device_state             ;E30C: 95 53          '.S'
        BNE     ZE319                    ;E30E: 26 09          '&.'
        BRA     ZE31F                    ;E310: 20 0D          ' .'

ZE312   ANDA    #$07                     ;E312: 84 07          '..'
        LSRA                             ;E314: 44             'D'
        BITA    device_state             ;E315: 95 53          '.S'
        BNE     ZE31F                    ;E317: 26 06          '&.'
ZE319   LDAA    device_state             ;E319: 96 53          '.S'
        ANDA    #$BF                     ;E31B: 84 BF          '..'
        STAA    device_state             ;E31D: 97 53          '.S'
ZE31F   LDAA    device_state             ;E31F: 96 53          '.S'
        ANDA    $01,X                    ;E321: A4 01          '..'
        ORAA    $02,X                    ;E323: AA 02          '..'
        STAA    device_state             ;E325: 97 53          '.S'
        LDAA    status_confirmed         ;E327: 96 55          '.U'
        ANDA    $03,X                    ;E329: A4 03          '..'
        ORAA    $04,X                    ;E32B: AA 04          '..'
        STAA    status_pending           ;E32D: 97 54          '.T'
        STAA    status_confirmed         ;E32F: 97 55          '.U'
        BRA     ZE360                    ;E331: 20 2D          ' -'

; Handle commands D-H (current limits)
ZE333   LDAA    acia_rx_cmd              ;E333: 96 39          '.9'
        SUBA    #$44                     ;E335: 80 44          '.D'
        CMPA    #$02                     ;E337: 81 02          '..'
        BLS     ZE33D                    ;E339: 23 02          '#.'
        SUBA    #$02                     ;E33B: 80 02          '..'
ZE33D   LDAB    acia_rx_cmd              ;E33D: D6 39          '.9'
        CMPB    #$46                     ;E33F: C1 46          '.F'
        BHI     ZE349                    ;E341: 22 06          '".'
        BITA    device_state             ;E343: 95 53          '.S'
        BNE     ZE34D                    ;E345: 26 06          '&.'
        BRA     ZE360                    ;E347: 20 17          ' .'

ZE349   BITA    device_state             ;E349: 95 53          '.S'
        BNE     ZE360                    ;E34B: 26 13          '&.'
ZE34D   LDX     #DAC_CLIP_TABLE_B        ;E34D: CE E3 8C       '...'
        STX     indirect_ptr_hi          ;E350: DF 5E          '.^'
        LDAA    acia_rx_cmd              ;E352: 96 39          '.9'
        SUBA    #$45                     ;E354: 80 45          '.E'
        ADDA    indirect_ptr_lo          ;E356: 9B 5F          '._'
        STAA    indirect_ptr_lo          ;E358: 97 5F          '._'
        LDX     indirect_ptr_hi          ;E35A: DE 5E          '.^'
        LDAA    ,X                       ;E35C: A6 00          '..'
        STAA    dac_update_mask          ;E35E: 97 66          '.f'
; Call dac_update_all to apply changes
ZE360   JSR     dac_update_all           ;E360: BD EB E2       '...'
        LDAA    device_state             ;E363: 96 53          '.S'
        BITA    #$80                     ;E365: 85 80          '..'
        BEQ     ZE375                    ;E367: 27 0C          ''.'
        ANDA    #$01                     ;E369: 84 01          '..'
        TAB                              ;E36B: 16             '.'
        ASLB                             ;E36C: 58             'X'
        ABA                              ;E36D: 1B             '.'
        LDAB    device_state             ;E36E: D6 53          '.S'
        ANDB    #$FC                     ;E370: C4 FC          '..'
        ABA                              ;E372: 1B             '.'
        STAA    device_state             ;E373: 97 53          '.S'
ZE375   JMP     cold_start_entry         ;E375: 7E E4 63       '~.c'

DAC_CLIP_TABLE_A FCC     " "                      ;E378: 20             ' '
        FCB     $FD,$02,$0F              ;E379: FD 02 0F       '...'
        FCC     "P"                      ;E37C: 50             'P'
        FCB     $02,$FE,$01,$F0,$05,$10  ;E37D: 02 FE 01 F0 05 10 '......'
        FCB     $FD,$00,$0F              ;E383: FD 00 0F       '...'
        FCC     "@"                      ;E386: 40             '@'
        FCB     $01,$FE,$00,$F0,$04      ;E387: 01 FE 00 F0 04 '.....'
DAC_CLIP_TABLE_B FCB     $04                      ;E38C: 04             '.'
        FCC     "@"                      ;E38D: 40             '@'
        FCB     $08,$80                  ;E38E: 08 80          '..'
cmd_set_reinit_flag LDAA    #$FF                     ;E390: 86 FF          '..'
        STAA    reinit_requested         ;E392: 97 42          '.B'
        JMP     cold_start_entry         ;E394: 7E E4 63       '~.c'

; === READ DAC CHANNEL ===
; Calculate register offset from channel index
cmd_read_dac_channel LDX     #cha_voltage_set_hi      ;E397: CE 00 06       '...'
        STX     indirect_ptr_hi          ;E39A: DF 5E          '.^'
        ADDA    indirect_ptr_lo          ;E39C: 9B 5F          '._'
        STAA    indirect_ptr_lo          ;E39E: 97 5F          '._'
        LDX     indirect_ptr_hi          ;E3A0: DE 5E          '.^'
; Load 16-bit DAC value
        LDAA    ,X                       ;E3A2: A6 00          '..'
        LDAB    $01,X                    ;E3A4: E6 01          '..'
; Right-shift (remove dirty bit)
        ANDA    #$7F                     ;E3A6: 84 7F          '..'
        LSRA                             ;E3A8: 44             'D'
        RORB                             ;E3A9: 56             'V'
; Store in TX buffer for response
        STAA    acia_tx_data_hi          ;E3AA: 97 3F          '.?'
        STAB    acia_tx_data_lo          ;E3AC: D7 40          '.@'
        RTS                              ;E3AE: 39             '9'

;-------------------------------------------------------------------------------

; === STORE AND CONVERT DAC VALUE ===
; Store received 16-bit value in DAC register
cmd_store_and_convert STX     indirect_ptr_hi          ;E3AF: DF 5E          '.^'
        TAB                              ;E3B1: 16             '.'
        ADDA    indirect_ptr_lo          ;E3B2: 9B 5F          '._'
        STAA    indirect_ptr_lo          ;E3B4: 97 5F          '._'
        LDX     indirect_ptr_hi          ;E3B6: DE 5E          '.^'
        LDAA    acia_rx_data_hi          ;E3B8: 96 3A          '.:'
        STAA    ,X                       ;E3BA: A7 00          '..'
        LDAA    acia_rx_data_lo          ;E3BC: 96 3B          '.;'
        STAA    $01,X                    ;E3BE: A7 01          '..'
        CMPB    #$02                     ;E3C0: C1 02          '..'
        BHI     ZE431                    ;E3C2: 22 6D          '"m'
        LDAB    dac_settle_timer         ;E3C4: D6 67          '.g'
        ANDB    #$E0                     ;E3C6: C4 E0          '..'
; Compare command against 'A'-'D' for channel routing
        LDAA    acia_rx_cmd              ;E3C8: 96 39          '.9'
        CMPA    #$41                     ;E3CA: 81 41          '.A'
        BEQ     ZE3DC                    ;E3CC: 27 0E          ''.'
        CMPA    #$42                     ;E3CE: 81 42          '.B'
        BEQ     ZE3F0                    ;E3D0: 27 1E          ''.'
        CMPA    #$43                     ;E3D2: 81 43          '.C'
        BEQ     ZE405                    ;E3D4: 27 2F          ''/'
        CMPA    #$44                     ;E3D6: 81 44          '.D'
        BEQ     ZE41A                    ;E3D8: 27 40          ''@'
        BRA     ZE431                    ;E3DA: 20 55          ' U'

; Handle 'A': clear ChA voltage shadow
ZE3DC   CLRA                             ;E3DC: 4F             'O'
        TST     >dac_settle_timer        ;E3DD: 7D 00 67       '}.g'
        BEQ     ZE3E8                    ;E3E0: 27 06          ''.'
        BITB    #$C0                     ;E3E2: C5 C0          '..'
        BEQ     ZE3E8                    ;E3E4: 27 02          ''.'
        ORAA    #$10                     ;E3E6: 8A 10          '..'
ZE3E8   CLR     >cha_vs_shadow_hi        ;E3E8: 7F 00 0E       '...'
        CLR     >cha_vs_shadow_lo        ;E3EB: 7F 00 0F       '...'
        BRA     ZE42D                    ;E3EE: 20 3D          ' ='

; Handle 'B': clear ChA current shadow
ZE3F0   LDAA    #$C0                     ;E3F0: 86 C0          '..'
        TST     >dac_settle_timer        ;E3F2: 7D 00 67       '}.g'
        BEQ     ZE3FD                    ;E3F5: 27 06          ''.'
        BITB    #$C0                     ;E3F7: C5 C0          '..'
        BNE     ZE3FD                    ;E3F9: 26 02          '&.'
        ORAA    #$10                     ;E3FB: 8A 10          '..'
ZE3FD   CLR     >chb_vs_shadow_hi        ;E3FD: 7F 00 1A       '...'
        CLR     >chb_vs_shadow_lo        ;E400: 7F 00 1B       '...'
        BRA     ZE42D                    ;E403: 20 28          ' ('

; Handle 'C': clear ChB voltage shadow
ZE405   LDAA    #$20                     ;E405: 86 20          '. '
        TST     >dac_settle_timer        ;E407: 7D 00 67       '}.g'
        BEQ     ZE412                    ;E40A: 27 06          ''.'
        BITB    #$C0                     ;E40C: C5 C0          '..'
        BEQ     ZE412                    ;E40E: 27 02          ''.'
        ORAA    #$10                     ;E410: 8A 10          '..'
ZE412   CLR     >cha_is_shadow_hi        ;E412: 7F 00 10       '...'
        CLR     >cha_is_shadow_lo        ;E415: 7F 00 11       '...'
        BRA     ZE42D                    ;E418: 20 13          ' .'

; Handle 'D': clear ChB current shadow
ZE41A   LDAA    #$E0                     ;E41A: 86 E0          '..'
        TST     >dac_settle_timer        ;E41C: 7D 00 67       '}.g'
        BEQ     ZE427                    ;E41F: 27 06          ''.'
        BITB    #$C0                     ;E421: C5 C0          '..'
        BNE     ZE427                    ;E423: 26 02          '&.'
        ORAA    #$10                     ;E425: 8A 10          '..'
ZE427   CLR     >chb_is_shadow_hi        ;E427: 7F 00 1C       '...'
        CLR     >chb_is_shadow_lo        ;E42A: 7F 00 1D       '...'
ZE42D   ORAA    #$06                     ;E42D: 8A 06          '..'
        STAA    dac_settle_timer         ;E42F: 97 67          '.g'
ZE431   RTS                              ;E431: 39             '9'

;-------------------------------------------------------------------------------

ME432_via_cvec_e167 LDAA    status_confirmed         ;E432: 96 55          '.U'
        ANDA    #$F0                     ;E434: 84 F0          '..'
        ORAA    #$02                     ;E436: 8A 02          '..'
        STAA    status_confirmed         ;E438: 97 55          '.U'
        STAA    status_pending           ;E43A: 97 54          '.T'
        JMP     cold_start_entry         ;E43C: 7E E4 63       '~.c'

ME43F_via_cvec_e169 LDAA    status_confirmed         ;E43F: 96 55          '.U'
        ANDA    #$0F                     ;E441: 84 0F          '..'
        ORAA    #$20                     ;E443: 8A 20          '. '
        STAA    status_confirmed         ;E445: 97 55          '.U'
        STAA    status_pending           ;E447: 97 54          '.T'
        JMP     cold_start_entry         ;E449: 7E E4 63       '~.c'

ME44C_via_cvec_e16b LDAA    status_confirmed         ;E44C: 96 55          '.U'
        ANDA    #$F0                     ;E44E: 84 F0          '..'
        ORAA    #$03                     ;E450: 8A 03          '..'
        STAA    status_confirmed         ;E452: 97 55          '.U'
        STAA    status_pending           ;E454: 97 54          '.T'
        JMP     cold_start_entry         ;E456: 7E E4 63       '~.c'

ME459_via_cvec_e16d LDAA    status_confirmed         ;E459: 96 55          '.U'
        ANDA    #$0F                     ;E45B: 84 0F          '..'
        ORAA    #$30                     ;E45D: 8A 30          '.0'
        STAA    status_confirmed         ;E45F: 97 55          '.U'
        STAA    status_pending           ;E461: 97 54          '.T'
; === COLD START (RESET handler) ===
; Disable interrupts, set stack pointer
cold_start_entry JMP     ZE14D                    ;E463: 7E E1 4D       '~.M'
; Disable IC19 CB2 interrupt
; === RESET HANDLER �¨ cold_start_entry ===
hdlr_RST SEI                              ;E466: 0F             '.'
        LDS     #M007F                   ;E467: 8E 00 7F       '...'
; Setup IC20 direction registers
        JSR     setup_ic20_directions    ;E46A: BD E5 DF       '...'
; Initialize ACIA with full reset
        JSR     acia_init_with_reset     ;E46D: BD E4 C5       '...'
; Read IC18 Port A (switch state)
        LDAA    IC18_PRA                 ;E470: 96 A0          '..'
        ORAA    #$0F                     ;E472: 8A 0F          '..'
; Set IC18 PA3:PA0 as outputs (DAC mux select)
        STAA    IC18_PRA                 ;E474: 97 A0          '..'
; Initialize DAC output system
        JSR     clear_ram_selective      ;E476: BD E5 F1       '...'
; Clear device_state, keycode, key_state_flags, frame_type
        CLR     >device_state            ;E479: 7F 00 53       '..S'
        CLR     >keycode_or_adcmode      ;E47C: 7F 00 43       '..C'
        CLR     >key_state_flags         ;E47F: 7F 00 44       '..D'
        CLR     >uart_frame_type         ;E482: 7F 00 56       '..V'
        CLRA                             ;E485: 4F             'O'
        CLRB                             ;E486: 5F             '_'
; Startup delay loop (~65536 iterations)
ZE487   DECB                             ;E487: 5A             'Z'
        BNE     ZE487                    ;E488: 26 FD          '&.'
        DECA                             ;E48A: 4A             'J'
        BNE     ZE487                    ;E48B: 26 FA          '&.'
; Set GPIB link active flag to 0xFF
        LDAA    #$FF                     ;E48D: 86 FF          '..'
        STAA    gpib_link_active         ;E48F: 97 41          '.A'
; Jump to post_init_setup
        JMP     post_init_setup          ;E491: 7E E5 21       '~.!'

; === WARM RESTART ===
; Disable interrupts, reload stack pointer
warm_restart SEI                              ;E494: 0F             '.'
        LDS     #M007F                   ;E495: 8E 00 7F       '...'
        LDAA    IC19_CRB                 ;E498: 96 E3          '..'
        ANDA    #$F7                     ;E49A: 84 F7          '..'
        STAA    IC19_CRB                 ;E49C: 97 E3          '..'
        LDAA    IC20_CRA                 ;E49E: 96 91          '..'
        ANDA    #$F7                     ;E4A0: 84 F7          '..'
        STAA    IC20_CRA                 ;E4A2: 97 91          '..'
; Setup IC20 direction registers
        JSR     setup_ic20_directions    ;E4A4: BD E5 DF       '...'
; Initialize ACIA (no master reset)
        JSR     acia_init_no_reset       ;E4A7: BD E4 C9       '...'
        LDAA    IC18_PRA                 ;E4AA: 96 A0          '..'
        ORAA    #$0F                     ;E4AC: 8A 0F          '..'
        STAA    IC18_PRA                 ;E4AE: 97 A0          '..'
        JSR     clear_ram_selective      ;E4B0: BD E5 F1       '...'
; Clear key state bits 6:5
        LDAA    key_state_flags          ;E4B3: 96 44          '.D'
        ANDA    #$5F                     ;E4B5: 84 5F          '._'
        STAA    key_state_flags          ;E4B7: 97 44          '.D'
; Check GPIB link status
        TST     >gpib_link_active        ;E4B9: 7D 00 41       '}.A'
        BNE     ZE4C2                    ;E4BC: 26 04          '&.'
        LDAA    #$FF                     ;E4BE: 86 FF          '..'
        STAA    gpib_link_active         ;E4C0: 97 41          '.A'
; Jump to post_init_setup
ZE4C2   JMP     post_init_setup          ;E4C2: 7E E5 21       '~.!'

; === ACIA INIT (with master reset) ===
; Write 0x13 to ACIA CSR (master reset)
acia_init_with_reset LDAA    #$13                     ;E4C5: 86 13          '..'
        STAA    ACIA_CSR                 ;E4C7: 97 D0          '..'
; Write 0x91: /16 clock, 8N2, RTS, RX interrupt enabled
acia_init_no_reset LDAA    #$91                     ;E4C9: 86 91          '..'
        STAA    ACIA_CSR                 ;E4CB: 97 D0          '..'
        LDAA    IC18_CRA                 ;E4CD: 96 A1          '..'
        ANDA    #$FB                     ;E4CF: 84 FB          '..'
; === PIA DIRECTION REGISTER SETUP ===
; IC18: PA3:PA0 outputs (DAC mux), PB inputs (ADC data)
        STAA    IC18_CRA                 ;E4D1: 97 A1          '..'
        LDAA    IC18_CRB                 ;E4D3: 96 A3          '..'
        ANDA    #$FB                     ;E4D5: 84 FB          '..'
        STAA    IC18_CRB                 ;E4D7: 97 A3          '..'
        LDAA    IC19_CRA                 ;E4D9: 96 E1          '..'
        ANDA    #$FB                     ;E4DB: 84 FB          '..'
        STAA    IC19_CRA                 ;E4DD: 97 E1          '..'
        LDAA    IC19_CRB                 ;E4DF: 96 E3          '..'
        ANDA    #$FB                     ;E4E1: 84 FB          '..'
        STAA    IC19_CRB                 ;E4E3: 97 E3          '..'
        LDAA    IC20_CRA                 ;E4E5: 96 91          '..'
        ANDA    #$FB                     ;E4E7: 84 FB          '..'
        STAA    IC20_CRA                 ;E4E9: 97 91          '..'
        LDAA    IC20_CRB                 ;E4EB: 96 93          '..'
        ANDA    #$FB                     ;E4ED: 84 FB          '..'
        STAA    IC20_CRB                 ;E4EF: 97 93          '..'
        LDAA    #$0F                     ;E4F1: 86 0F          '..'
        STAA    IC18_PRA                 ;E4F3: 97 A0          '..'
        CLRA                             ;E4F5: 4F             'O'
        STAA    IC18_PRB                 ;E4F6: 97 A2          '..'
        LDAA    #$FF                     ;E4F8: 86 FF          '..'
; IC19: PA outputs (keyboard column drive), PB4:5 outputs
        STAA    IC19_PRA                 ;E4FA: 97 E0          '..'
        LDAA    #$30                     ;E4FC: 86 30          '.0'
        STAA    IC19_PRB                 ;E4FE: 97 E2          '..'
        LDAA    #$FF                     ;E500: 86 FF          '..'
; IC20: PA and PB all outputs (display/segment drive)
        STAA    IC20_PRA                 ;E502: 97 90          '..'
        LDAA    #$FF                     ;E504: 86 FF          '..'
        STAA    IC20_PRB                 ;E506: 97 92          '..'
        LDAA    #$3C                     ;E508: 86 3C          '.<'
; IC18 CA2 High (DAC latch strobe)
        STAA    IC18_CRA                 ;E50A: 97 A1          '..'
        LDAA    #$35                     ;E50C: 86 35          '.5'
; IC19 CA2 Low + CA1 IRQ enabled (keyboard interrupt)
        STAA    IC19_CRA                 ;E50E: 97 E1          '..'
        LDAA    #$34                     ;E510: 86 34          '.4'
        STAA    IC20_CRA                 ;E512: 97 91          '..'
        LDAA    #$34                     ;E514: 86 34          '.4'
; IC18/IC19/IC20 CB2 Low (various control signals)
        STAA    IC18_CRB                 ;E516: 97 A3          '..'
        LDAA    #$34                     ;E518: 86 34          '.4'
        STAA    IC19_CRB                 ;E51A: 97 E3          '..'
        LDAA    #$34                     ;E51C: 86 34          '.4'
        STAA    IC20_CRB                 ;E51E: 97 93          '..'
        RTS                              ;E520: 39             '9'

;-------------------------------------------------------------------------------

; === POST-INIT SETUP ===
; Init watchdog to 0xFF, prescaler to 4
post_init_setup LDAA    #$FF                     ;E521: 86 FF          '..'
        STAA    watchdog_counter         ;E523: 97 04          '..'
        LDAA    #$04                     ;E525: 86 04          '..'
        STAA    irq_prescaler            ;E527: 97 00          '..'
; Clear DAC output registers
        CLRA                             ;E529: 4F             'O'
        STAA    dac_out_cha_v            ;E52A: 97 24          '.$'
        STAA    dac_out_cha_i            ;E52C: 97 25          '.%'
        STAA    dac_out_chb_v            ;E52E: 97 26          '.&'
        STAA    dac_out_chb_i            ;E530: 97 27          '.''
; Init DAC latch to 0x80 (midscale)
        LDAA    #$80                     ;E532: 86 80          '..'
        STAA    DAC_LATCH                ;E534: 97 80          '..'
        STAA    dac_out_cha_vl           ;E536: 97 28          '.('
        STAA    dac_out_cha_il           ;E538: 97 29          '.)'
        STAA    dac_out_chb_vl           ;E53A: 97 2A          '.*'
        STAA    dac_out_chb_il           ;E53C: 97 2B          '.+'
; Init status to 0x44 (both channels idle)
        LDAA    #$44                     ;E53E: 86 44          '.D'
        STAA    status_confirmed         ;E540: 97 55          '.U'
        STAA    status_pending           ;E542: 97 54          '.T'
; Read SW3.1 to determine range mode
        LDAA    IC18_PRA                 ;E544: 96 A0          '..'
; SW3.1: selects between 25V/2A (0x1130) and 50V/1A (0x0898)
        BITA    #$10                     ;E546: 85 10          '..'
        BNE     ZE54F                    ;E548: 26 05          '&.'
        LDX     #range_threshold_25V     ;E54A: CE 11 30       '..0'
        BRA     ZE552                    ;E54D: 20 03          ' .'

ZE54F   LDX     #range_threshold_50V     ;E54F: CE 08 98       '...'
; Store range threshold in current limit registers
ZE552   STX     cha_current_limit_hi     ;E552: DF 0C          '..'
        STX     chb_current_limit_hi     ;E554: DF 18          '..'
; Set initial DAC update mask to 0x99
        LDAA    #$99                     ;E556: 86 99          '..'
        STAA    dac_update_mask          ;E558: 97 66          '.f'
        LDX     #chb_current_set_hi      ;E55A: CE 00 14       '...'
        STX     cha_voltage_limit_hi     ;E55D: DF 0A          '..'
        STX     chb_voltage_limit_hi     ;E55F: DF 16          '..'
; Enable interrupts, enter main loop
        CLI                              ;E561: 0E             '.'
        JMP     main_loop                ;E562: 7E E5 7A       '~.z'

; === IRQ DISPATCHER ===
; Check IC19 CRA bit 7 (keyboard interrupt pending)
hdlr_IRQ LDAA    #$80                     ;E565: 86 80          '..'
        BITA    IC19_CRA                 ;E567: 95 E1          '..'
; Branch if not keyboard: check ACIA
        BEQ     ZE570                    ;E569: 27 05          ''.'
; Keyboard IRQ: jump to keyboard handler
        JMP     hdlr_KB_IRQ              ;E56B: 7E EA 60       '~.`'

ZE56E   BRA     hdlr_RTI                 ;E56E: 20 09          ' .'

; Check ACIA CSR bit 7 (ACIA interrupt pending)
ZE570   BITA    ACIA_CSR                 ;E570: 95 D0          '..'
        BEQ     hdlr_RTI                 ;E572: 27 05          ''.'
; ACIA IRQ: jump to ACIA handler
        JMP     hdlr_ACIA_IRQ            ;E574: 7E E0 00       '~..'

        BRA     hdlr_RTI                 ;E577: 20 00          ' .'

; RTI (no interrupt source found)
hdlr_RTI RTI                              ;E579: 3B             ';'
; === MAIN LOOP ===
; Reset prescaler counter
main_loop LDAA    #$14                     ;E57A: 86 14          '..'
        STAA    watchdog_counter         ;E57C: 97 04          '..'
; Check reinit flag
        TST     >reinit_requested        ;E57E: 7D 00 42       '}.B'
        BEQ     ZE58D                    ;E581: 27 0A          ''.'
; Clear reinit flag, set link active, warm restart
        CLR     >reinit_requested        ;E583: 7F 00 42       '..B'
        LDAA    #$FF                     ;E586: 86 FF          '..'
        STAA    gpib_link_active         ;E588: 97 41          '.A'
        JMP     warm_restart             ;E58A: 7E E4 94       '~..'

; Decrement status send delay if nonzero
ZE58D   LDAA    status_send_delay        ;E58D: 96 64          '.d'
        BEQ     main_loop_body           ;E58F: 27 03          ''.'
        DEC     >status_send_delay       ;E591: 7A 00 64       'z.d'
; Call: keyboard scan
main_loop_body JSR     keyboard_scan_entry      ;E594: BD EE 07       '...'
; Call: ADC read and process
        JSR     adc_read_and_process     ;E597: BD EF 22       '.."'
; Call: ADC acquisition
        JSR     adc_acquire_reading      ;E59A: BD F8 13       '...'
; Call: DAC-from-ADC update
        JSR     update_dac_from_adc      ;E59D: BD F9 C2       '...'
; Call: process output and status
        JSR     process_output_and_status ;E5A0: BD E7 BA       '...'
; Decrement ACIA inhibit timer
        LDAA    acia_inhibit_timer       ;E5A3: 96 63          '.c'
        BEQ     ZE5AA                    ;E5A5: 27 03          ''.'
        DEC     >acia_inhibit_timer      ;E5A7: 7A 00 63       'z.c'
ZE5AA   NOP                              ;E5AA: 01             '.'
        LDAA    status_send_delay        ;E5AB: 96 64          '.d'
        BNE     ZE5CF                    ;E5AD: 26 20          '& '
; === STATUS SEND PHASE (alternating between two types) ===
        SEI                              ;E5AF: 0F             '.'
; Toggle status_toggle flag
        COM     >status_toggle           ;E5B0: 73 00 65       's.e'
; If toggle=0: send device_state with 0x20 framing
        BNE     ZE5C4                    ;E5B3: 26 0F          '&.'
        LDAB    device_state             ;E5B5: D6 53          '.S'
        ANDB    #$CF                     ;E5B7: C4 CF          '..'
        ORAB    #$20                     ;E5B9: CA 20          '. '
        JSR     acia_send_byte           ;E5BB: BD E0 99       '...'
        LDAA    #$0E                     ;E5BE: 86 0E          '..'
        STAA    status_send_delay        ;E5C0: 97 64          '.d'
        BRA     ZE5CF                    ;E5C2: 20 0B          ' .'

; If toggle=1: send frame_type with 0x30 framing
ZE5C4   LDAB    uart_frame_type          ;E5C4: D6 56          '.V'
        ORAB    #$30                     ;E5C6: CA 30          '.0'
        JSR     acia_send_byte           ;E5C8: BD E0 99       '...'
; Set status send delay to 0x0E
        LDAA    #$0E                     ;E5CB: 86 0E          '..'
        STAA    status_send_delay        ;E5CD: 97 64          '.d'
; Enable interrupts
ZE5CF   CLI                              ;E5CF: 0E             '.'
; Toggle IC18 CB2 (ADC clock/strobe cycle)
        LDAA    IC18_CRB                 ;E5D0: 96 A3          '..'
        ANDA    #$F7                     ;E5D2: 84 F7          '..'
        STAA    IC18_CRB                 ;E5D4: 97 A3          '..'
        LDAA    IC18_CRB                 ;E5D6: 96 A3          '..'
        ORAA    #$08                     ;E5D8: 8A 08          '..'
        STAA    IC18_CRB                 ;E5DA: 97 A3          '..'
; Loop back to main_loop
        JMP     main_loop                ;E5DC: 7E E5 7A       '~.z'

setup_ic20_directions LDAA    IC20_CRA                 ;E5DF: 96 91          '..'
        ANDA    #$FB                     ;E5E1: 84 FB          '..'
        STAA    IC20_CRA                 ;E5E3: 97 91          '..'
        CLR     >IC20_PRA                ;E5E5: 7F 00 90       '...'
        ORAA    #$04                     ;E5E8: 8A 04          '..'
        STAA    IC20_CRA                 ;E5EA: 97 91          '..'
        LDAA    #$08                     ;E5EC: 86 08          '..'
        STAA    IC20_PRA                 ;E5EE: 97 90          '..'
        RTS                              ;E5F0: 39             '9'

;-------------------------------------------------------------------------------

clear_ram_selective LDX     #display_scan_index      ;E5F1: CE 00 68       '..h'
ZE5F4   CPX     #output_update_pending   ;E5F4: 8C 00 03       '...'
        BEQ     ZE623                    ;E5F7: 27 2A          ''*'
        CPX     #gpib_link_active        ;E5F9: 8C 00 41       '..A'
        BEQ     ZE623                    ;E5FC: 27 25          ''%'
        CPX     #uart_frame_type         ;E5FE: 8C 00 56       '..V'
        BEQ     ZE623                    ;E601: 27 20          '' '
        CPX     #acia_tx_cmd             ;E603: 8C 00 3E       '..>'
        BEQ     ZE623                    ;E606: 27 1B          ''.'
        CPX     #acia_tx_data_hi         ;E608: 8C 00 3F       '..?'
        BEQ     ZE623                    ;E60B: 27 16          ''.'
        CPX     #acia_tx_data_lo         ;E60D: 8C 00 40       '..@'
        BEQ     ZE623                    ;E610: 27 11          ''.'
        CPX     #reinit_requested        ;E612: 8C 00 42       '..B'
        BEQ     ZE623                    ;E615: 27 0C          ''.'
        CPX     #key_state_flags         ;E617: 8C 00 44       '..D'
        BEQ     ZE623                    ;E61A: 27 07          ''.'
        CPX     #keycode_or_adcmode      ;E61C: 8C 00 43       '..C'
        BEQ     ZE623                    ;E61F: 27 02          ''.'
        CLR     ,X                       ;E621: 6F 00          'o.'
ZE623   DEX                              ;E623: 09             '.'
        BNE     ZE5F4                    ;E624: 26 CE          '&.'
        CLR     ,X                       ;E626: 6F 00          'o.'
        RTS                              ;E628: 39             '9'

;-------------------------------------------------------------------------------

; === NMI HANDLER ===
hdlr_NMI SEI                              ;E629: 0F             '.'
        LDAB    #$4A                     ;E62A: C6 4A          '.J'
        JSR     acia_send_byte           ;E62C: BD E0 99       '...'
        JMP     hdlr_RST                 ;E62F: 7E E4 66       '~.f'

; === SWI HANDLER (watchdog timeout) ===
hdlr_SWI SEI                              ;E632: 0F             '.'
        LDAB    #$49                     ;E633: C6 49          '.I'
        JSR     acia_send_byte           ;E635: BD E0 99       '...'
        JMP     hdlr_RST                 ;E638: 7E E4 66       '~.f'

control_loop_channel_a LDAA    gpib_link_active         ;E63B: 96 41          '.A'
        BEQ     ZE645                    ;E63D: 27 06          ''.'
        JSR     init_feedback_registers  ;E63F: BD E7 7D       '..}'
        JMP     ZE715                    ;E642: 7E E7 15       '~..'

ZE645   LDAA    status_pending           ;E645: 96 54          '.T'
        ANDA    #$0F                     ;E647: 84 0F          '..'
        CMPA    #$0F                     ;E649: 81 0F          '..'
        BNE     ZE660                    ;E64B: 26 13          '&.'
        SEI                              ;E64D: 0F             '.'
        LDX     digit_buf_0              ;E64E: DE 4B          '.K'
        STX     cha_fb_voltage_hi        ;E650: DF 2F          './'
        LDX     digit_buf_2              ;E652: DE 4D          '.M'
        STX     cha_fb_current_hi        ;E654: DF 31          '.1'
        LDX     #chb_fb_voltage_hi       ;E656: CE 00 33       '..3'
        JSR     set_dac_dirty_flags      ;E659: BD E7 17       '...'
        CLI                              ;E65C: 0E             '.'
        JMP     control_loop_channel_b   ;E65D: 7E E6 B6       '~..'

ZE660   ASLA                             ;E660: 48             'H'
        LDX     #cha_voltage_set_hi      ;E661: CE 00 06       '...'
        STX     temp_ptr_hi              ;E664: DF 5B          '.['
        ADDA    temp_ptr_lo              ;E666: 9B 5C          '.\'
        STAA    temp_ptr_lo              ;E668: 97 5C          '.\'
        LDAA    temp_ptr_hi              ;E66A: 96 5B          '.['
        ADCA    #$00                     ;E66C: 89 00          '..'
        STAA    temp_ptr_hi              ;E66E: 97 5B          '.['
        LDX     temp_ptr_hi              ;E670: DE 5B          '.['
        JSR     scale_and_output_dac     ;E672: BD E7 26       '..&'
        SEI                              ;E675: 0F             '.'
        LDAA    dac_settle_timer         ;E676: 96 67          '.g'
        BEQ     ZE69C                    ;E678: 27 22          ''"'
        BITA    #$10                     ;E67A: 85 10          '..'
        BNE     ZE684                    ;E67C: 26 06          '&.'
        ANDA    #$EF                     ;E67E: 84 EF          '..'
        CMPA    #$2F                     ;E680: 81 2F          './'
        BHI     ZE69C                    ;E682: 22 18          '".'
ZE684   LDX     #M8F8F                   ;E684: CE 8F 8F       '...'
        STX     cha_fb_voltage_hi        ;E687: DF 2F          './'
        STX     cha_fb_current_hi        ;E689: DF 31          '.1'
        LDAA    dac_settle_timer         ;E68B: 96 67          '.g'
        BITA    #$10                     ;E68D: 85 10          '..'
        BNE     ZE695                    ;E68F: 26 04          '&.'
        LDAA    device_state             ;E691: 96 53          '.S'
        BPL     ZE6B5                    ;E693: 2A 20          '* '
ZE695   STX     chb_fb_voltage_hi        ;E695: DF 33          '.3'
        STX     chb_fb_current_hi        ;E697: DF 35          '.5'
        JMP     ZE715                    ;E699: 7E E7 15       '~..'

ZE69C   LDX     #cha_fb_voltage_hi       ;E69C: CE 00 2F       '../'
        JSR     load_adc_digits_to_buffer ;E69F: BD E7 36       '..6'
        LDX     #cha_fb_voltage_hi       ;E6A2: CE 00 2F       '../'
        CLRA                             ;E6A5: 4F             'O'
        JSR     check_dac_limits         ;E6A6: BD E7 4F       '..O'
        LDAA    status_pending           ;E6A9: 96 54          '.T'
        RORA                             ;E6AB: 46             'F'
        BCS     control_loop_channel_b   ;E6AC: 25 08          '%.'
        SEI                              ;E6AE: 0F             '.'
        LDAA    cha_fb_voltage_lo        ;E6AF: 96 30          '.0'
        ORAA    #$80                     ;E6B1: 8A 80          '..'
        STAA    cha_fb_voltage_lo        ;E6B3: 97 30          '.0'
ZE6B5   CLI                              ;E6B5: 0E             '.'
control_loop_channel_b LDAA    status_pending           ;E6B6: 96 54          '.T'
        ANDA    #$F0                     ;E6B8: 84 F0          '..'
        CMPA    #$F0                     ;E6BA: 81 F0          '..'
        BNE     ZE6D1                    ;E6BC: 26 13          '&.'
        SEI                              ;E6BE: 0F             '.'
        LDX     digit_buf_0              ;E6BF: DE 4B          '.K'
        STX     chb_fb_voltage_hi        ;E6C1: DF 33          '.3'
        LDX     digit_buf_2              ;E6C3: DE 4D          '.M'
        STX     chb_fb_current_hi        ;E6C5: DF 35          '.5'
        LDX     #uart_timeout_lo         ;E6C7: CE 00 37       '..7'
        JSR     set_dac_dirty_flags      ;E6CA: BD E7 17       '...'
        CLI                              ;E6CD: 0E             '.'
        JMP     ZE715                    ;E6CE: 7E E7 15       '~..'

ZE6D1   CLI                              ;E6D1: 0E             '.'
        ASRA                             ;E6D2: 47             'G'
        ASRA                             ;E6D3: 47             'G'
        ASRA                             ;E6D4: 47             'G'
        LDX     #chb_voltage_set_hi      ;E6D5: CE 00 12       '...'
        STX     temp_ptr_hi              ;E6D8: DF 5B          '.['
        ADDA    temp_ptr_lo              ;E6DA: 9B 5C          '.\'
        STAA    temp_ptr_lo              ;E6DC: 97 5C          '.\'
        LDAA    temp_ptr_hi              ;E6DE: 96 5B          '.['
        ADCA    #$00                     ;E6E0: 89 00          '..'
        STAA    temp_ptr_hi              ;E6E2: 97 5B          '.['
        LDX     temp_ptr_hi              ;E6E4: DE 5B          '.['
        JSR     scale_and_output_dac     ;E6E6: BD E7 26       '..&'
        SEI                              ;E6E9: 0F             '.'
        LDAA    dac_settle_timer         ;E6EA: 96 67          '.g'
        ANDA    #$E0                     ;E6EC: 84 E0          '..'
        CMPA    #$20                     ;E6EE: 81 20          '. '
        BLS     ZE6FB                    ;E6F0: 23 09          '#.'
        LDX     #M8F8F                   ;E6F2: CE 8F 8F       '...'
        STX     chb_fb_voltage_hi        ;E6F5: DF 33          '.3'
        STX     chb_fb_current_hi        ;E6F7: DF 35          '.5'
        BRA     ZE715                    ;E6F9: 20 1A          ' .'

ZE6FB   LDX     #chb_fb_voltage_hi       ;E6FB: CE 00 33       '..3'
        JSR     load_adc_digits_to_buffer ;E6FE: BD E7 36       '..6'
        LDX     #chb_fb_voltage_hi       ;E701: CE 00 33       '..3'
        LDAA    #$FF                     ;E704: 86 FF          '..'
        JSR     check_dac_limits         ;E706: BD E7 4F       '..O'
        LDAA    status_pending           ;E709: 96 54          '.T'
        BITA    #$10                     ;E70B: 85 10          '..'
        BNE     ZE715                    ;E70D: 26 06          '&.'
        LDAA    chb_fb_voltage_lo        ;E70F: 96 34          '.4'
        ORAA    #$80                     ;E711: 8A 80          '..'
        STAA    chb_fb_voltage_lo        ;E713: 97 34          '.4'
ZE715   CLI                              ;E715: 0E             '.'
        RTS                              ;E716: 39             '9'

;-------------------------------------------------------------------------------

set_dac_dirty_flags LDAB    digit_count              ;E717: D6 50          '.P'
        BEQ     ZE725                    ;E719: 27 0A          ''.'
ZE71B   DEX                              ;E71B: 09             '.'
        DECB                             ;E71C: 5A             'Z'
        BNE     ZE71B                    ;E71D: 26 FC          '&.'
        LDAA    ,X                       ;E71F: A6 00          '..'
        ORAA    #$80                     ;E721: 8A 80          '..'
        STAA    ,X                       ;E723: A7 00          '..'
ZE725   RTS                              ;E725: 39             '9'

;-------------------------------------------------------------------------------

scale_and_output_dac LDAA    ,X                       ;E726: A6 00          '..'
        LDAB    $01,X                    ;E728: E6 01          '..'
        ANDA    #$7F                     ;E72A: 84 7F          '..'
        ASRA                             ;E72C: 47             'G'
        RORB                             ;E72D: 56             'V'
        STAA    math_work_hi             ;E72E: 97 59          '.Y'
        STAB    math_work_lo             ;E730: D7 5A          '.Z'
        JSR     binary_to_bcd            ;E732: BD EB 41       '..A'
        RTS                              ;E735: 39             '9'

;-------------------------------------------------------------------------------

load_adc_digits_to_buffer LDAA    adc_digit_1              ;E736: 96 1F          '..'
        ANDA    #$0F                     ;E738: 84 0F          '..'
        STAA    ,X                       ;E73A: A7 00          '..'
        LDAA    adc_digit_2              ;E73C: 96 20          '. '
        ANDA    #$0F                     ;E73E: 84 0F          '..'
        STAA    $01,X                    ;E740: A7 01          '..'
        LDAA    adc_digit_3              ;E742: 96 21          '.!'
        ANDA    #$0F                     ;E744: 84 0F          '..'
        STAA    $02,X                    ;E746: A7 02          '..'
        LDAA    adc_digit_4              ;E748: 96 22          '."'
        ANDA    #$0F                     ;E74A: 84 0F          '..'
        STAA    $03,X                    ;E74C: A7 03          '..'
        RTS                              ;E74E: 39             '9'

;-------------------------------------------------------------------------------

check_dac_limits LDAB    #$0F                     ;E74F: C6 0F          '..'
        TSTA                             ;E751: 4D             'M'
        BNE     ZE75C                    ;E752: 26 08          '&.'
        LDAA    status_pending           ;E754: 96 54          '.T'
        BITA    #$01                     ;E756: 85 01          '..'
        BNE     ZE76A                    ;E758: 26 10          '&.'
        BRA     ZE762                    ;E75A: 20 06          ' .'

ZE75C   LDAA    status_pending           ;E75C: 96 54          '.T'
        BITA    #$10                     ;E75E: 85 10          '..'
        BNE     ZE76A                    ;E760: 26 08          '&.'
ZE762   LDAA    ,X                       ;E762: A6 00          '..'
        BNE     ZE77C                    ;E764: 26 16          '&.'
        STAB    ,X                       ;E766: E7 00          '..'
        BRA     ZE77C                    ;E768: 20 12          ' .'

ZE76A   LDAA    ,X                       ;E76A: A6 00          '..'
        BNE     ZE77C                    ;E76C: 26 0E          '&.'
        STAB    ,X                       ;E76E: E7 00          '..'
        LDAA    $01,X                    ;E770: A6 01          '..'
        BNE     ZE77C                    ;E772: 26 08          '&.'
        STAB    $01,X                    ;E774: E7 01          '..'
        LDAA    $02,X                    ;E776: A6 02          '..'
        BNE     ZE77C                    ;E778: 26 02          '&.'
        STAB    $02,X                    ;E77A: E7 02          '..'
ZE77C   RTS                              ;E77C: 39             '9'

;-------------------------------------------------------------------------------

init_feedback_registers SEI                              ;E77D: 0F             '.'
        LDX     #M0F0F                   ;E77E: CE 0F 0F       '...'
        STX     cha_fb_voltage_hi        ;E781: DF 2F          './'
        STX     cha_fb_current_hi        ;E783: DF 31          '.1'
        STX     chb_fb_voltage_hi        ;E785: DF 33          '.3'
        STX     chb_fb_current_hi        ;E787: DF 35          '.5'
        CLRB                             ;E789: 5F             '_'
        LDAA    gpib_link_active         ;E78A: 96 41          '.A'
        CMPA    #$FF                     ;E78C: 81 FF          '..'
        BEQ     ZE7B2                    ;E78E: 27 22          ''"'
        BITA    #$08                     ;E790: 85 08          '..'
        BEQ     ZE796                    ;E792: 27 02          ''.'
        LDAB    #$0B                     ;E794: C6 0B          '..'
ZE796   ANDA    #$07                     ;E796: 84 07          '..'
        STAB    cha_fb_voltage_lo        ;E798: D7 30          '.0'
        STAA    cha_fb_current_hi        ;E79A: 97 31          '.1'
        CLRB                             ;E79C: 5F             '_'
        LDAA    gpib_link_active         ;E79D: 96 41          '.A'
        BITA    #$80                     ;E79F: 85 80          '..'
        BEQ     ZE7A5                    ;E7A1: 27 02          ''.'
        LDAB    #$0B                     ;E7A3: C6 0B          '..'
ZE7A5   ANDA    #$70                     ;E7A5: 84 70          '.p'
        ASRA                             ;E7A7: 47             'G'
        ASRA                             ;E7A8: 47             'G'
        ASRA                             ;E7A9: 47             'G'
        ASRA                             ;E7AA: 47             'G'
        STAB    chb_fb_voltage_lo        ;E7AB: D7 34          '.4'
        STAA    chb_fb_current_hi        ;E7AD: 97 35          '.5'
        CLI                              ;E7AF: 0E             '.'
        BRA     ZE7B9                    ;E7B0: 20 07          ' .'

ZE7B2   LDX     #irq_prescaler           ;E7B2: CE 00 00       '...'
        STX     cha_fb_voltage_lo        ;E7B5: DF 30          '.0'
        STX     chb_fb_voltage_lo        ;E7B7: DF 34          '.4'
ZE7B9   RTS                              ;E7B9: 39             '9'

;-------------------------------------------------------------------------------

; === PROCESS OUTPUT AND STATUS ===
; Calls control loop and display update functions
process_output_and_status NOP                              ;E7BA: 01             '.'
        NOP                              ;E7BB: 01             '.'
        JSR     control_loop_channel_a   ;E7BC: BD E6 3B       '..;'
        JSR     update_display_and_leds  ;E7BF: BD E7 C6       '...'
        NOP                              ;E7C2: 01             '.'
        NOP                              ;E7C3: 01             '.'
        NOP                              ;E7C4: 01             '.'
        RTS                              ;E7C5: 39             '9'

;-------------------------------------------------------------------------------

; === UPDATE DISPLAY AND LEDS ===
; Clear working registers
update_display_and_leds CLR     >temp_ptr_hi             ;E7C6: 7F 00 5B       '..['
        CLR     >temp_ptr_lo             ;E7C9: 7F 00 5C       '..\'
        CLR     >temp_counter            ;E7CC: 7F 00 5D       '..]'
; Check frame_type: bit 7 = mode change pending
        LDAA    uart_frame_type          ;E7CF: 96 56          '.V'
        BPL     ZE7DA                    ;E7D1: 2A 07          '*.'
; Mode change: update LED via channel 1
        LDAA    #$01                     ;E7D3: 86 01          '..'
        JSR     clear_led_bit            ;E7D5: BD EA 4B       '..K'
        BRA     ZE7E3                    ;E7D8: 20 09          ' .'

; Normal: check frame_type bit 0, update LED via channel 1
ZE7DA   BITA    #$01                     ;E7DA: 85 01          '..'
        BEQ     ZE7E3                    ;E7DC: 27 05          ''.'
        LDAA    #$01                     ;E7DE: 86 01          '..'
        JSR     set_led_bit              ;E7E0: BD EA 46       '..F'
; Check M0x52 bit 6: update LED via channel 2
ZE7E3   LDAA    cmd_flags                ;E7E3: 96 52          '.R'
        BITA    #$40                     ;E7E5: 85 40          '.@'
        BEQ     ZE7F0                    ;E7E7: 27 07          ''.'
        LDAA    #$02                     ;E7E9: 86 02          '..'
        JSR     clear_led_bit            ;E7EB: BD EA 4B       '..K'
        BRA     ZE7FB                    ;E7EE: 20 0B          ' .'

; Check frame_type bit 1: update LED via channel 2
ZE7F0   LDAA    uart_frame_type          ;E7F0: 96 56          '.V'
        BITA    #$02                     ;E7F2: 85 02          '..'
        BEQ     ZE7FB                    ;E7F4: 27 05          ''.'
        LDAA    #$02                     ;E7F6: 86 02          '..'
        JSR     set_led_bit              ;E7F8: BD EA 46       '..F'
; Check M0x52 bit 5: update LED via channel 8
ZE7FB   LDAA    cmd_flags                ;E7FB: 96 52          '.R'
        BITA    #$20                     ;E7FD: 85 20          '. '
        BEQ     ZE808                    ;E7FF: 27 07          ''.'
        LDAA    #$08                     ;E801: 86 08          '..'
        JSR     clear_led_bit            ;E803: BD EA 4B       '..K'
        BRA     ZE811                    ;E806: 20 09          ' .'

; Check device_state bit 7 (tracking): update LED via channel 8
ZE808   LDAA    device_state             ;E808: 96 53          '.S'
        BPL     ZE811                    ;E80A: 2A 05          '*.'
        LDAA    #$08                     ;E80C: 86 08          '..'
        JSR     set_led_bit              ;E80E: BD EA 46       '..F'
; === CHANNEL MODE LED INDICATORS ===
; Check device_state bits for CV/CC/VL/IL mode combinations
; Set/clear corresponding indicator LEDs via IC19 Port B
ZE811   LDAA    device_state             ;E811: 96 53          '.S'
        ANDA    #$05                     ;E813: 84 05          '..'
        CMPA    #$05                     ;E815: 81 05          '..'
        BEQ     ZE82B                    ;E817: 27 12          ''.'
        LDAA    device_state             ;E819: 96 53          '.S'
        ANDA    #$0A                     ;E81B: 84 0A          '..'
        CMPA    #$0A                     ;E81D: 81 0A          '..'
        BEQ     ZE82B                    ;E81F: 27 0A          ''.'
        LDAA    device_state             ;E821: 96 53          '.S'
        ANDA    #$0F                     ;E823: 84 0F          '..'
        CMPA    #$0F                     ;E825: 81 0F          '..'
        BEQ     ZE82B                    ;E827: 27 02          ''.'
        BRA     ZE830                    ;E829: 20 05          ' .'

; Both channels in same mode �¨ specific LED pattern
ZE82B   LDAA    #$10                     ;E82B: 86 10          '..'
        JSR     clear_led_bit            ;E82D: BD EA 4B       '..K'
ZE830   LDAA    channel_mode_state       ;E830: 96 51          '.Q'
        ANDA    #$8B                     ;E832: 84 8B          '..'
        CMPA    #$89                     ;E834: 81 89          '..'
        BEQ     ZE84D                    ;E836: 27 15          ''.'
        CMPA    #$8A                     ;E838: 81 8A          '..'
        BEQ     ZE84D                    ;E83A: 27 11          ''.'
        LDAA    status_pending           ;E83C: 96 54          '.T'
        TAB                              ;E83E: 16             '.'
        ANDA    #$0F                     ;E83F: 84 0F          '..'
        ANDB    #$F0                     ;E841: C4 F0          '..'
        CMPA    #$02                     ;E843: 81 02          '..'
        BEQ     ZE84D                    ;E845: 27 06          ''.'
        CMPB    #$20                     ;E847: C1 20          '. '
        BEQ     ZE84D                    ;E849: 27 02          ''.'
        BRA     ZE852                    ;E84B: 20 05          ' .'

ZE84D   LDAA    #$10                     ;E84D: 86 10          '..'
        JSR     set_led_bit              ;E84F: BD EA 46       '..F'
ZE852   LDAA    device_state             ;E852: 96 53          '.S'
        ANDA    #$05                     ;E854: 84 05          '..'
        CMPA    #$04                     ;E856: 81 04          '..'
        BEQ     ZE86C                    ;E858: 27 12          ''.'
        LDAA    device_state             ;E85A: 96 53          '.S'
        ANDA    #$0A                     ;E85C: 84 0A          '..'
        CMPA    #$08                     ;E85E: 81 08          '..'
        BEQ     ZE86C                    ;E860: 27 0A          ''.'
        LDAA    device_state             ;E862: 96 53          '.S'
        ANDA    #$0F                     ;E864: 84 0F          '..'
        CMPA    #$0C                     ;E866: 81 0C          '..'
        BEQ     ZE86C                    ;E868: 27 02          ''.'
        BRA     ZE871                    ;E86A: 20 05          ' .'

ZE86C   LDAA    #$20                     ;E86C: 86 20          '. '
        JSR     clear_led_bit            ;E86E: BD EA 4B       '..K'
ZE871   LDAA    channel_mode_state       ;E871: 96 51          '.Q'
        ANDA    #$93                     ;E873: 84 93          '..'
        CMPA    #$91                     ;E875: 81 91          '..'
        BEQ     ZE88E                    ;E877: 27 15          ''.'
        CMPA    #$92                     ;E879: 81 92          '..'
        BEQ     ZE88E                    ;E87B: 27 11          ''.'
        LDAA    status_pending           ;E87D: 96 54          '.T'
        TAB                              ;E87F: 16             '.'
        ANDA    #$0F                     ;E880: 84 0F          '..'
        ANDB    #$F0                     ;E882: C4 F0          '..'
        CMPA    #$03                     ;E884: 81 03          '..'
        BEQ     ZE88E                    ;E886: 27 06          ''.'
        CMPB    #$30                     ;E888: C1 30          '.0'
        BEQ     ZE88E                    ;E88A: 27 02          ''.'
        BRA     ZE893                    ;E88C: 20 05          ' .'

ZE88E   LDAA    #$20                     ;E88E: 86 20          '. '
        JSR     set_led_bit              ;E890: BD EA 46       '..F'
ZE893   SEI                              ;E893: 0F             '.'
        LDAA    uart_timeout_lo          ;E894: 96 37          '.7'
        ANDA    temp_ptr_hi              ;E896: 94 5B          '.['
        ORAA    temp_ptr_lo              ;E898: 9A 5C          '.\'
        LDAB    output_update_pending    ;E89A: D6 03          '..'
        BEQ     ZE8A0                    ;E89C: 27 02          ''.'
        BRA     ZE8A6                    ;E89E: 20 06          ' .'

ZE8A0   EORA    temp_ptr_hi              ;E8A0: 98 5B          '.['
        LDAB    #$FF                     ;E8A2: C6 FF          '..'
        STAB    temp_counter             ;E8A4: D7 5D          '.]'
ZE8A6   STAA    uart_timeout_lo          ;E8A6: 97 37          '.7'
        CLI                              ;E8A8: 0E             '.'
        CLR     >temp_ptr_hi             ;E8A9: 7F 00 5B       '..['
        CLR     >temp_ptr_lo             ;E8AC: 7F 00 5C       '..\'
        LDAA    status_pending           ;E8AF: 96 54          '.T'
        ANDA    #$0F                     ;E8B1: 84 0F          '..'
        BEQ     ZE8D0                    ;E8B3: 27 1B          ''.'
        CMPA    #$04                     ;E8B5: 81 04          '..'
        BEQ     ZE8C9                    ;E8B7: 27 10          ''.'
        CMPA    #$02                     ;E8B9: 81 02          '..'
        BEQ     ZE8C9                    ;E8BB: 27 0C          ''.'
        CMPA    #$0F                     ;E8BD: 81 0F          '..'
        BNE     ZE8D7                    ;E8BF: 26 16          '&.'
        LDAA    channel_mode_state       ;E8C1: 96 51          '.Q'
        ANDA    #$09                     ;E8C3: 84 09          '..'
        CMPA    #$09                     ;E8C5: 81 09          '..'
        BNE     ZE8D7                    ;E8C7: 26 0E          '&.'
ZE8C9   LDAA    #$01                     ;E8C9: 86 01          '..'
        JSR     set_led_bit              ;E8CB: BD EA 46       '..F'
        BRA     ZE8FF                    ;E8CE: 20 2F          ' /'

ZE8D0   LDAA    #$01                     ;E8D0: 86 01          '..'
        JSR     clear_led_bit            ;E8D2: BD EA 4B       '..K'
        BRA     ZE8FF                    ;E8D5: 20 28          ' ('

ZE8D7   LDAA    status_pending           ;E8D7: 96 54          '.T'
        ANDA    #$0F                     ;E8D9: 84 0F          '..'
        CMPA    #$05                     ;E8DB: 81 05          '..'
        BEQ     ZE8F3                    ;E8DD: 27 14          ''.'
        CMPA    #$01                     ;E8DF: 81 01          '..'
        BEQ     ZE8FA                    ;E8E1: 27 17          ''.'
        CMPA    #$03                     ;E8E3: 81 03          '..'
        BEQ     ZE8F3                    ;E8E5: 27 0C          ''.'
        CMPA    #$0F                     ;E8E7: 81 0F          '..'
        BNE     ZE8FF                    ;E8E9: 26 14          '&.'
        LDAA    channel_mode_state       ;E8EB: 96 51          '.Q'
        ANDA    #$11                     ;E8ED: 84 11          '..'
        CMPA    #$11                     ;E8EF: 81 11          '..'
        BNE     ZE8FF                    ;E8F1: 26 0C          '&.'
ZE8F3   LDAA    #$02                     ;E8F3: 86 02          '..'
        JSR     set_led_bit              ;E8F5: BD EA 46       '..F'
        BRA     ZE8FF                    ;E8F8: 20 05          ' .'

ZE8FA   LDAA    #$02                     ;E8FA: 86 02          '..'
        JSR     clear_led_bit            ;E8FC: BD EA 4B       '..K'
ZE8FF   LDAA    status_pending           ;E8FF: 96 54          '.T'
        ANDA    #$F0                     ;E901: 84 F0          '..'
        CMPA    #$40                     ;E903: 81 40          '.@'
        BEQ     ZE91B                    ;E905: 27 14          ''.'
        CMPA    #$00                     ;E907: 81 00          '..'
        BEQ     ZE922                    ;E909: 27 17          ''.'
        CMPA    #$20                     ;E90B: 81 20          '. '
        BEQ     ZE91B                    ;E90D: 27 0C          ''.'
        CMPA    #$F0                     ;E90F: 81 F0          '..'
        BNE     ZE929                    ;E911: 26 16          '&.'
        LDAA    channel_mode_state       ;E913: 96 51          '.Q'
        ANDA    #$0A                     ;E915: 84 0A          '..'
        CMPA    #$0A                     ;E917: 81 0A          '..'
        BNE     ZE929                    ;E919: 26 0E          '&.'
ZE91B   LDAA    #$04                     ;E91B: 86 04          '..'
        JSR     set_led_bit              ;E91D: BD EA 46       '..F'
        BRA     ZE951                    ;E920: 20 2F          ' /'

ZE922   LDAA    #$04                     ;E922: 86 04          '..'
        JSR     clear_led_bit            ;E924: BD EA 4B       '..K'
        BRA     ZE951                    ;E927: 20 28          ' ('

ZE929   LDAA    status_pending           ;E929: 96 54          '.T'
        ANDA    #$F0                     ;E92B: 84 F0          '..'
        CMPA    #$50                     ;E92D: 81 50          '.P'
        BEQ     ZE945                    ;E92F: 27 14          ''.'
        CMPA    #$10                     ;E931: 81 10          '..'
        BEQ     ZE94C                    ;E933: 27 17          ''.'
        CMPA    #$30                     ;E935: 81 30          '.0'
        BEQ     ZE945                    ;E937: 27 0C          ''.'
        CMPA    #$F0                     ;E939: 81 F0          '..'
        BNE     ZE951                    ;E93B: 26 14          '&.'
        LDAA    channel_mode_state       ;E93D: 96 51          '.Q'
        ANDA    #$12                     ;E93F: 84 12          '..'
        CMPA    #$12                     ;E941: 81 12          '..'
        BNE     ZE951                    ;E943: 26 0C          '&.'
ZE945   LDAA    #$08                     ;E945: 86 08          '..'
        JSR     set_led_bit              ;E947: BD EA 46       '..F'
        BRA     ZE951                    ;E94A: 20 05          ' .'

ZE94C   LDAA    #$08                     ;E94C: 86 08          '..'
        JSR     clear_led_bit            ;E94E: BD EA 4B       '..K'
ZE951   LDAA    device_state             ;E951: 96 53          '.S'
        ANDA    #$05                     ;E953: 84 05          '..'
        BEQ     ZE961                    ;E955: 27 0A          ''.'
        CMPA    #$01                     ;E957: 81 01          '..'
        BEQ     ZE96F                    ;E959: 27 14          ''.'
        CMPA    #$04                     ;E95B: 81 04          '..'
        BEQ     ZE976                    ;E95D: 27 17          ''.'
        BRA     ZE968                    ;E95F: 20 07          ' .'

ZE961   LDAA    #$10                     ;E961: 86 10          '..'
        JSR     set_led_bit              ;E963: BD EA 46       '..F'
        BRA     ZE97B                    ;E966: 20 13          ' .'

ZE968   LDAA    #$10                     ;E968: 86 10          '..'
        JSR     clear_led_bit            ;E96A: BD EA 4B       '..K'
        BRA     ZE97B                    ;E96D: 20 0C          ' .'

ZE96F   LDAA    #$20                     ;E96F: 86 20          '. '
        JSR     set_led_bit              ;E971: BD EA 46       '..F'
        BRA     ZE97B                    ;E974: 20 05          ' .'

ZE976   LDAA    #$20                     ;E976: 86 20          '. '
        JSR     clear_led_bit            ;E978: BD EA 4B       '..K'
ZE97B   LDAA    device_state             ;E97B: 96 53          '.S'
        ANDA    #$0A                     ;E97D: 84 0A          '..'
        BEQ     ZE98B                    ;E97F: 27 0A          ''.'
        CMPA    #$02                     ;E981: 81 02          '..'
        BEQ     ZE999                    ;E983: 27 14          ''.'
        CMPA    #$08                     ;E985: 81 08          '..'
        BEQ     ZE9A0                    ;E987: 27 17          ''.'
        BRA     ZE992                    ;E989: 20 07          ' .'

ZE98B   LDAA    #$40                     ;E98B: 86 40          '.@'
        JSR     set_led_bit              ;E98D: BD EA 46       '..F'
        BRA     ZE9A5                    ;E990: 20 13          ' .'

ZE992   LDAA    #$40                     ;E992: 86 40          '.@'
        JSR     clear_led_bit            ;E994: BD EA 4B       '..K'
        BRA     ZE9A5                    ;E997: 20 0C          ' .'

ZE999   LDAA    #$80                     ;E999: 86 80          '..'
        JSR     set_led_bit              ;E99B: BD EA 46       '..F'
        BRA     ZE9A5                    ;E99E: 20 05          ' .'

ZE9A0   LDAA    #$80                     ;E9A0: 86 80          '..'
        JSR     clear_led_bit            ;E9A2: BD EA 4B       '..K'
ZE9A5   SEI                              ;E9A5: 0F             '.'
        LDAA    uart_timeout_hi          ;E9A6: 96 38          '.8'
        ANDA    temp_ptr_hi              ;E9A8: 94 5B          '.['
        ORAA    temp_ptr_lo              ;E9AA: 9A 5C          '.\'
        LDAB    output_update_pending    ;E9AC: D6 03          '..'
        BEQ     ZE9B2                    ;E9AE: 27 02          ''.'
        BRA     ZE9B8                    ;E9B0: 20 06          ' .'

ZE9B2   EORA    temp_ptr_hi              ;E9B2: 98 5B          '.['
        LDAB    #$FF                     ;E9B4: C6 FF          '..'
        STAB    temp_counter             ;E9B6: D7 5D          '.]'
ZE9B8   STAA    uart_timeout_hi          ;E9B8: 97 38          '.8'
        CLI                              ;E9BA: 0E             '.'
        LDAA    device_state             ;E9BB: 96 53          '.S'
        BITA    #$40                     ;E9BD: 85 40          '.@'
        BNE     ZE9C9                    ;E9BF: 26 08          '&.'
        LDAA    IC19_CRA                 ;E9C1: 96 E1          '..'
        ANDA    #$F7                     ;E9C3: 84 F7          '..'
        STAA    IC19_CRA                 ;E9C5: 97 E1          '..'
        BRA     ZE9CF                    ;E9C7: 20 06          ' .'

ZE9C9   LDAA    IC19_CRA                 ;E9C9: 96 E1          '..'
        ORAA    #$08                     ;E9CB: 8A 08          '..'
        STAA    IC19_CRA                 ;E9CD: 97 E1          '..'
ZE9CF   LDAB    cmd_flags                ;E9CF: D6 52          '.R'
        ANDB    #$80                     ;E9D1: C4 80          '..'
        LDAA    channel_mode_state       ;E9D3: 96 51          '.Q'
        ANDA    #$03                     ;E9D5: 84 03          '..'
        ABA                              ;E9D7: 1B             '.'
        TAB                              ;E9D8: 16             '.'
        LDAA    #$CF                     ;E9D9: 86 CF          '..'
        STAA    temp_ptr_hi              ;E9DB: 97 5B          '.['
        STAA    temp_ptr_lo              ;E9DD: 97 5C          '.\'
        CMPB    #$80                     ;E9DF: C1 80          '..'
        BEQ     ZEA19                    ;E9E1: 27 36          ''6'
        CMPB    #$81                     ;E9E3: C1 81          '..'
        BEQ     ZE9FD                    ;E9E5: 27 16          ''.'
        CMPB    #$82                     ;E9E7: C1 82          '..'
        BEQ     ZEA04                    ;E9E9: 27 19          ''.'
        CMPB    #$01                     ;E9EB: C1 01          '..'
        BEQ     ZEA0B                    ;E9ED: 27 1C          ''.'
        CMPB    #$02                     ;E9EF: C1 02          '..'
        BEQ     ZEA12                    ;E9F1: 27 1F          ''.'
        CMPB    #$03                     ;E9F3: C1 03          '..'
        BEQ     ZEA20                    ;E9F5: 27 29          '')'
        CMPB    #$83                     ;E9F7: C1 83          '..'
        BEQ     ZEA19                    ;E9F9: 27 1E          ''.'
        BRA     ZEA25                    ;E9FB: 20 28          ' ('

ZE9FD   LDAA    #$20                     ;E9FD: 86 20          '. '
        JSR     clear_led_bit            ;E9FF: BD EA 4B       '..K'
        BRA     ZEA25                    ;EA02: 20 21          ' !'

ZEA04   LDAA    #$10                     ;EA04: 86 10          '..'
        JSR     clear_led_bit            ;EA06: BD EA 4B       '..K'
        BRA     ZEA25                    ;EA09: 20 1A          ' .'

ZEA0B   LDAA    #$20                     ;EA0B: 86 20          '. '
        JSR     set_led_bit              ;EA0D: BD EA 46       '..F'
        BRA     ZEA25                    ;EA10: 20 13          ' .'

ZEA12   LDAA    #$10                     ;EA12: 86 10          '..'
        JSR     set_led_bit              ;EA14: BD EA 46       '..F'
        BRA     ZEA25                    ;EA17: 20 0C          ' .'

ZEA19   LDAA    #$30                     ;EA19: 86 30          '.0'
        JSR     clear_led_bit            ;EA1B: BD EA 4B       '..K'
        BRA     ZEA25                    ;EA1E: 20 05          ' .'

ZEA20   LDAA    #$30                     ;EA20: 86 30          '.0'
        JSR     set_led_bit              ;EA22: BD EA 46       '..F'
ZEA25   LDAA    IC19_PRB                 ;EA25: 96 E2          '..'
        ANDA    temp_ptr_hi              ;EA27: 94 5B          '.['
        ORAA    temp_ptr_lo              ;EA29: 9A 5C          '.\'
        LDAB    output_update_pending    ;EA2B: D6 03          '..'
        BEQ     ZEA31                    ;EA2D: 27 02          ''.'
        BRA     ZEA3D                    ;EA2F: 20 0C          ' .'

ZEA31   LDAB    temp_ptr_hi              ;EA31: D6 5B          '.['
        ANDB    #$30                     ;EA33: C4 30          '.0'
        STAB    temp_ptr_hi              ;EA35: D7 5B          '.['
        EORA    temp_ptr_hi              ;EA37: 98 5B          '.['
        LDAB    #$FF                     ;EA39: C6 FF          '..'
        STAB    temp_counter             ;EA3B: D7 5D          '.]'
ZEA3D   STAA    IC19_PRB                 ;EA3D: 97 E2          '..'
        DEC     >output_update_pending   ;EA3F: 7A 00 03       'z..'
        JSR     check_update_pending     ;EA42: BD EA 50       '..P'
        RTS                              ;EA45: 39             '9'

;-------------------------------------------------------------------------------

; === SET LED BIT: OR into M005C ===
set_led_bit ORAA    temp_ptr_lo              ;EA46: 9A 5C          '.\'
        STAA    temp_ptr_lo              ;EA48: 97 5C          '.\'
        RTS                              ;EA4A: 39             '9'

;-------------------------------------------------------------------------------

; === CLEAR LED BIT: OR into M005B ===
clear_led_bit ORAA    temp_ptr_hi              ;EA4B: 9A 5B          '.['
        STAA    temp_ptr_hi              ;EA4D: 97 5B          '.['
        RTS                              ;EA4F: 39             '9'

;-------------------------------------------------------------------------------

; === CHECK IF OUTPUT UPDATE NEEDED ===
check_update_pending TST     >temp_counter            ;EA50: 7D 00 5D       '}.]'
        BEQ     ZEA59                    ;EA53: 27 04          ''.'
        LDAB    #$40                     ;EA55: C6 40          '.@'
        STAB    output_update_pending    ;EA57: D7 03          '..'
ZEA59   RTS                              ;EA59: 39             '9'

;-------------------------------------------------------------------------------

        LDAA    #$01                     ;EA5A: 86 01          '..'
ZEA5C   DECA                             ;EA5C: 4A             'J'
        BNE     ZEA5C                    ;EA5D: 26 FD          '&.'
        RTS                              ;EA5F: 39             '9'

;-------------------------------------------------------------------------------

; === KEYBOARD IRQ HANDLER ===
; Read IC19 Port A (keyboard matrix)
hdlr_KB_IRQ LDAA    IC19_PRA                 ;EA60: 96 E0          '..'
; Update DAC outputs (refresh during IRQ)
        JSR     dac_update_all           ;EA62: BD EB E2       '...'
; Advance DAC mux to next channel
        JSR     dac_mux_advance          ;EA65: BD FB 42       '..B'
; Write DAC output step
        JSR     dac_mux_output_step      ;EA68: BD FB 21       '..!'
; Process IRQ tick timing
        JSR     irq_tick_handler         ;EA6B: BD EA 74       '..t'
; Jump to output relay control
        JMP     output_relay_control     ;EA6E: 7E FB F7       '~..'

ZEA71   JMP     display_write_segment    ;EA71: 7E EA A2       '~..'

; === IRQ TICK HANDLER ===
; Decrement prescaler, reset to 4 when zero
irq_tick_handler DEC     >irq_prescaler           ;EA74: 7A 00 00       'z..'
        BNE     ZEA91                    ;EA77: 26 18          '&.'
        LDAA    #$04                     ;EA79: 86 04          '..'
        STAA    irq_prescaler            ;EA7B: 97 00          '..'
; Increment tick counter
        INC     >tick_counter            ;EA7D: 7C 00 05       '|..'
; Decrement debounce timer if nonzero
        TST     >debounce_timer          ;EA80: 7D 00 01       '}..'
        BEQ     ZEA88                    ;EA83: 27 03          ''.'
        DEC     >debounce_timer          ;EA85: 7A 00 01       'z..'
; Decrement watchdog, SWI if reaches zero
ZEA88   TST     >output_update_pending   ;EA88: 7D 00 03       '}..'
        DEC     >watchdog_counter        ;EA8B: 7A 00 04       'z..'
        BNE     ZEA91                    ;EA8E: 26 01          '&.'
        SWI                              ;EA90: 3F             '?'

; Decrement key repeat timer if nonzero
ZEA91   TST     >key_repeat_timer        ;EA91: 7D 00 02       '}..'
        BEQ     ZEA99                    ;EA94: 27 03          ''.'
        DEC     >key_repeat_timer        ;EA96: 7A 00 02       'z..'
; Decrement ACIA inhibit timer if nonzero
ZEA99   TST     >acia_inhibit_timer      ;EA99: 7D 00 63       '}.c'
        BEQ     ZEAA1                    ;EA9C: 27 03          ''.'
        DEC     >acia_inhibit_timer      ;EA9E: 7A 00 63       'z.c'
ZEAA1   RTS                              ;EAA1: 39             '9'

;-------------------------------------------------------------------------------

; === WRITE SEGMENT TO DISPLAY ===
; Build display address from scan index
display_write_segment LDAB    display_port_shadow      ;EAA2: D6 58          '.X'
        ANDB    #$C0                     ;EAA4: C4 C0          '..'
        ORAB    #$08                     ;EAA6: CA 08          '..'
        STAB    IC20_PRA                 ;EAA8: D7 90          '..'
        LDAA    display_scan_index       ;EAAA: 96 68          '.h'
        ORAA    #$10                     ;EAAC: 8A 10          '..'
        TAP                              ;EAAE: 06             '.'
        BCS     ZEAB6                    ;EAAF: 25 05          '%.'
        JMP     ZEB00                    ;EAB1: 7E EB 00       '~..'

        BRA     ZEAB9                    ;EAB4: 20 03          ' .'

ZEAB6   JMP     ZEB0A                    ;EAB6: 7E EB 0A       '~..'

ZEAB9   LDAA    display_scan_index       ;EAB9: 96 68          '.h'
        LDX     #cha_fb_voltage_hi       ;EABB: CE 00 2F       '../'
        DEX                              ;EABE: 09             '.'
        ADDA    #$01                     ;EABF: 8B 01          '..'
ZEAC1   INX                              ;EAC1: 08             '.'
        DECA                             ;EAC2: 4A             'J'
        BNE     ZEAC1                    ;EAC3: 26 FC          '&.'
        LDAA    ,X                       ;EAC5: A6 00          '..'
        BPL     ZEADC                    ;EAC7: 2A 13          '*.'
        ANDA    #$7F                     ;EAC9: 84 7F          '..'
; Lookup segment pattern in SEGMENT_MAP_TABLE
        LDX     #SEGMENT_MAP_TABLE       ;EACB: CE EB 21       '..!'
ZEACE   CMPA    ,X                       ;EACE: A1 00          '..'
        BEQ     ZEAD6                    ;EAD0: 27 04          ''.'
        INX                              ;EAD2: 08             '.'
        INX                              ;EAD3: 08             '.'
        BRA     ZEACE                    ;EAD4: 20 F8          ' .'

ZEAD6   LDAA    $01,X                    ;EAD6: A6 01          '..'
        ORAA    #$80                     ;EAD8: 8A 80          '..'
        BRA     ZEAE9                    ;EADA: 20 0D          ' .'

ZEADC   LDX     #SEGMENT_MAP_TABLE       ;EADC: CE EB 21       '..!'
ZEADF   CMPA    ,X                       ;EADF: A1 00          '..'
        BEQ     ZEAE7                    ;EAE1: 27 04          ''.'
        INX                              ;EAE3: 08             '.'
        INX                              ;EAE4: 08             '.'
        BRA     ZEADF                    ;EAE5: 20 F8          ' .'

ZEAE7   LDAA    $01,X                    ;EAE7: A6 01          '..'
; Write segment data to IC20 Port B
ZEAE9   ORAB    display_scan_index       ;EAE9: DA 68          '.h'
        STAA    IC20_PRB                 ;EAEB: 97 92          '..'
; Write address to IC20 Port A
        STAB    IC20_PRA                 ;EAED: D7 90          '..'
        STAB    display_port_shadow      ;EAEF: D7 58          '.X'
        LDAA    display_scan_index       ;EAF1: 96 68          '.h'
        ANDA    #$0F                     ;EAF3: 84 0F          '..'
; Advance scan index (0-6, wrapping)
        INCA                             ;EAF5: 4C             'L'
        CMPA    #$07                     ;EAF6: 81 07          '..'
        BLS     ZEAFB                    ;EAF8: 23 01          '#.'
        CLRA                             ;EAFA: 4F             'O'
ZEAFB   STAA    display_scan_index       ;EAFB: 97 68          '.h'
        JMP     ZE56E                    ;EAFD: 7E E5 6E       '~.n'

ZEB00   LDAA    uart_timeout_lo          ;EB00: 96 37          '.7'
        STAA    IC20_PRB                 ;EB02: 97 92          '..'
        LDAB    display_port_shadow      ;EB04: D6 58          '.X'
        ANDB    #$C0                     ;EB06: C4 C0          '..'
        BRA     ZEB14                    ;EB08: 20 0A          ' .'

ZEB0A   LDAA    uart_timeout_hi          ;EB0A: 96 38          '.8'
        STAA    IC20_PRB                 ;EB0C: 97 92          '..'
        LDAB    display_port_shadow      ;EB0E: D6 58          '.X'
        ANDB    #$C0                     ;EB10: C4 C0          '..'
        ORAB    #$10                     ;EB12: CA 10          '..'
ZEB14   LDAA    IC20_CRB                 ;EB14: 96 93          '..'
        ORAA    #$08                     ;EB16: 8A 08          '..'
        STAA    IC20_CRB                 ;EB18: 97 93          '..'
        ANDA    #$F7                     ;EB1A: 84 F7          '..'
        STAA    IC20_CRB                 ;EB1C: 97 93          '..'
        JMP     ZEAB9                    ;EB1E: 7E EA B9       '~..'

SEGMENT_MAP_TABLE FCB     $00                      ;EB21: 00             '.'     7-segment lookup table: maps digit value to segment pattern
        FCC     "?"                      ;EB22: 3F             '?'
        FCB     $01,$06,$02              ;EB23: 01 06 02       '...'
        FCC     "["                      ;EB26: 5B             '['
        FCB     $03                      ;EB27: 03             '.'
        FCC     "O"                      ;EB28: 4F             'O'
        FCB     $04                      ;EB29: 04             '.'
        FCC     "f"                      ;EB2A: 66             'f'
        FCB     $05                      ;EB2B: 05             '.'
        FCC     "m"                      ;EB2C: 6D             'm'
        FCB     $06                      ;EB2D: 06             '.'
        FCC     "}"                      ;EB2E: 7D             '}'
        FCB     $07,$07,$08,$7F,$09      ;EB2F: 07 07 08 7F 09 '.....'
        FCC     "o"                      ;EB34: 6F             'o'
        FCB     $0A,$08,$0B              ;EB35: 0A 08 0B       '...'
        FCC     "y"                      ;EB38: 79             'y'
        FCB     $0C                      ;EB39: 0C             '.'
        FCC     "v"                      ;EB3A: 76             'v'
        FCB     $0D                      ;EB3B: 0D             '.'
        FCC     "8"                      ;EB3C: 38             '8'
        FCB     $0E                      ;EB3D: 0E             '.'
        FCC     "s"                      ;EB3E: 73             's'
        FCB     $0F,$00                  ;EB3F: 0F 00          '..'
; === BINARY TO BCD (16-bit to 5 decimal digits) ===
; Clear digit buffer (M0x1E-M0x22)
binary_to_bcd LDX     #irq_prescaler           ;EB41: CE 00 00       '...'
        STX     adc_digit_0              ;EB44: DF 1E          '..'
        STX     adc_digit_2              ;EB46: DF 20          '. '
        CLRA                             ;EB48: 4F             'O'
        STAA    adc_digit_4              ;EB49: 97 22          '."'
        JMP     divide_by_powers_of_ten  ;EB4B: 7E EB A3       '~..'

; Mask each digit to lower nibble (BCD)
bcd_mask_digits LDX     #adc_digit_0             ;EB4E: CE 00 1E       '...'
        LDAB    #$05                     ;EB51: C6 05          '..'
ZEB53   LDAA    ,X                       ;EB53: A6 00          '..'
        ANDA    #$0F                     ;EB55: 84 0F          '..'
        STAA    ,X                       ;EB57: A7 00          '..'
        INX                              ;EB59: 08             '.'
        DECB                             ;EB5A: 5A             'Z'
        BNE     ZEB53                    ;EB5B: 26 F6          '&.'
        RTS                              ;EB5D: 39             '9'

;-------------------------------------------------------------------------------

; === MULTIPLY-ACCUMULATE (for BCD conversion) ===
; 16-bit multiply using shift-and-add
multiply_accumulate STAA    temp_counter             ;EB5E: 97 5D          '.]'
        CLR     >math_work_hi            ;EB60: 7F 00 59       '..Y'
        CLR     >math_work_lo            ;EB63: 7F 00 5A       '..Z'
        BRA     ZEB8B                    ;EB66: 20 23          ' #'

multiply_step LDAB    #$20                     ;EB68: C6 20          '. '
        LDAA    math_work_hi             ;EB6A: 96 59          '.Y'
        STAA    temp_ptr_hi              ;EB6C: 97 5B          '.['
        LDAA    math_work_lo             ;EB6E: 96 5A          '.Z'
        STAA    temp_ptr_lo              ;EB70: 97 5C          '.\'
ZEB72   ASL     >math_work_lo            ;EB72: 78 00 5A       'x.Z'
        ROL     >math_work_hi            ;EB75: 79 00 59       'y.Y'
        ASLB                             ;EB78: 58             'X'
        BEQ     ZEB8B                    ;EB79: 27 10          ''.'
        BPL     ZEB72                    ;EB7B: 2A F5          '*.'
        LDAA    math_work_lo             ;EB7D: 96 5A          '.Z'
        ADDA    temp_ptr_lo              ;EB7F: 9B 5C          '.\'
        STAA    math_work_lo             ;EB81: 97 5A          '.Z'
        LDAA    math_work_hi             ;EB83: 96 59          '.Y'
        ADCA    temp_ptr_hi              ;EB85: 99 5B          '.['
        STAA    math_work_hi             ;EB87: 97 59          '.Y'
        BRA     ZEB72                    ;EB89: 20 E7          ' .'

ZEB8B   LDAA    ,X                       ;EB8B: A6 00          '..'
        ADDA    math_work_lo             ;EB8D: 9B 5A          '.Z'
        STAA    math_work_lo             ;EB8F: 97 5A          '.Z'
        LDAA    math_work_hi             ;EB91: 96 59          '.Y'
        ADCA    #$00                     ;EB93: 89 00          '..'
        STAA    math_work_hi             ;EB95: 97 59          '.Y'
        BCC     ZEB9C                    ;EB97: 24 03          '$.'
        INC     >math_work_hi            ;EB99: 7C 00 59       '|.Y'
ZEB9C   INX                              ;EB9C: 08             '.'
        DEC     >temp_counter            ;EB9D: 7A 00 5D       'z.]'
        BNE     multiply_step            ;EBA0: 26 C6          '&.'
        RTS                              ;EBA2: 39             '9'

;-------------------------------------------------------------------------------

; === DIVIDE BY POWERS OF TEN ===
; Repeated subtraction of 10000, 1000, 100, 10
; Results in individual BCD digits
divide_by_powers_of_ten LDX     #adc_digit_0             ;EBA3: CE 00 1E       '...'
        LDAA    #$04                     ;EBA6: 86 04          '..'
        STAA    temp_counter             ;EBA8: 97 5D          '.]'
        LDAA    math_work_hi             ;EBAA: 96 59          '.Y'
        LDAB    math_work_lo             ;EBAC: D6 5A          '.Z'
        STX     math_work_hi             ;EBAE: DF 59          '.Y'
        LDX     #POWERS_OF_TEN           ;EBB0: CE EB DA       '...'
ZEBB3   SUBB    $01,X                    ;EBB3: E0 01          '..'
        SBCA    ,X                       ;EBB5: A2 00          '..'
        BPL     ZEBC9                    ;EBB7: 2A 10          '*.'
        ADDB    $01,X                    ;EBB9: EB 01          '..'
        ADCA    ,X                       ;EBBB: A9 00          '..'
        INX                              ;EBBD: 08             '.'
        INX                              ;EBBE: 08             '.'
        INC     >math_work_lo            ;EBBF: 7C 00 5A       '|.Z'
        DEC     >temp_counter            ;EBC2: 7A 00 5D       'z.]'
        BNE     ZEBB3                    ;EBC5: 26 EC          '&.'
        BRA     ZEBD3                    ;EBC7: 20 0A          ' .'

ZEBC9   STX     temp_ptr_hi              ;EBC9: DF 5B          '.['
        LDX     math_work_hi             ;EBCB: DE 59          '.Y'
        INC     ,X                       ;EBCD: 6C 00          'l.'
        LDX     temp_ptr_hi              ;EBCF: DE 5B          '.['
        BRA     ZEBB3                    ;EBD1: 20 E0          ' .'

ZEBD3   LDX     math_work_hi             ;EBD3: DE 59          '.Y'
        STAB    ,X                       ;EBD5: E7 00          '..'
        JMP     bcd_mask_digits          ;EBD7: 7E EB 4E       '~.N'

POWERS_OF_TEN FCC     "'"                      ;EBDA: 27             '''     Powers of ten: $2710(10000) $03E8(1000) $0064(100) $000A(10)
        FCB     $10,$03,$E8,$00          ;EBDB: 10 03 E8 00    '....'
        FCC     "d"                      ;EBDF: 64             'd'
        FCB     $00,$0A                  ;EBE0: 00 0A          '..'
; === DAC UPDATE ALL (process dac_update_mask) ===
; Check each bit of M0x66 (dac_update_mask)
; Bit 0: ChA voltage set �¨ scale and output
dac_update_all LDAA    dac_update_mask          ;EBE2: 96 66          '.f'
        BNE     ZEBE9                    ;EBE4: 26 03          '&.'
        JMP     ZEC7C                    ;EBE6: 7E EC 7C       '~.|'
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
